Adium1000/Octoglow/.github/frame (1).png

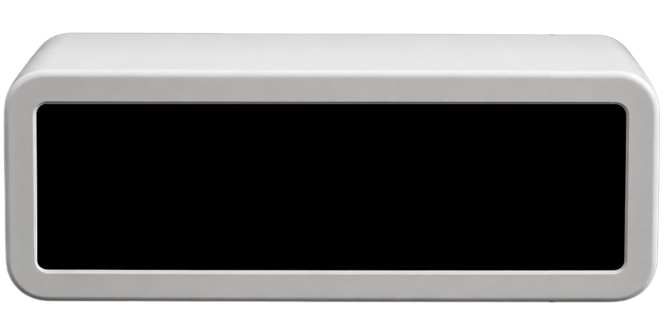
.github/frame (1).png
