Adium1000/Octoglow/.github/frame (2).png

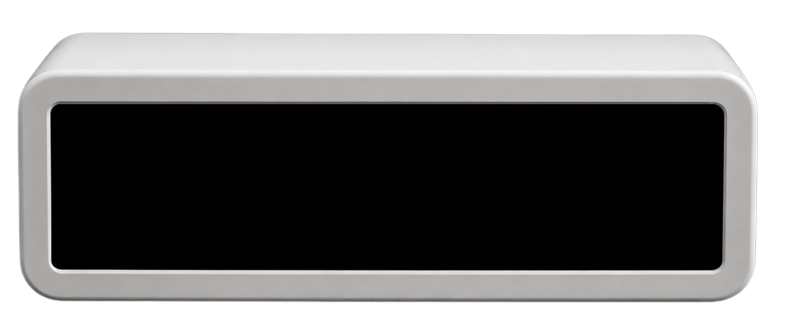
.github/frame (2).png
