Adium1000/Octoglow/.github/frame (3).png

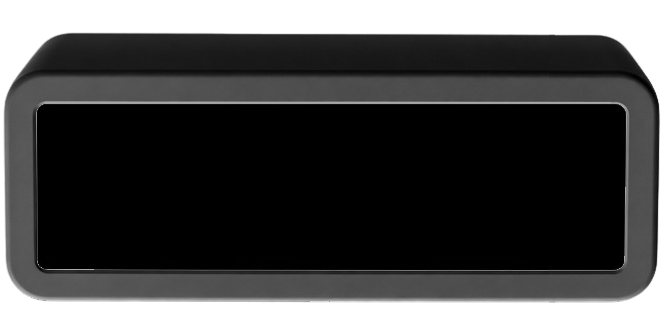
.github/frame (3).png
