Adium1000/Octoglow/Web/ER.png

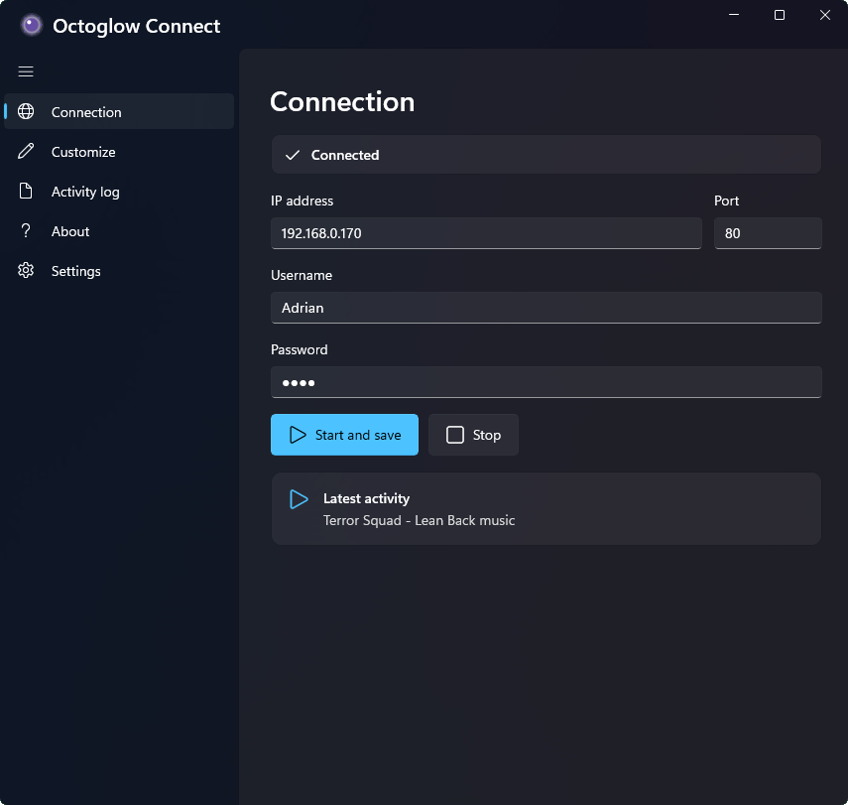
Web/ER.png
