Adium1000/Octoglow/Web/Octoglow_Clock.png

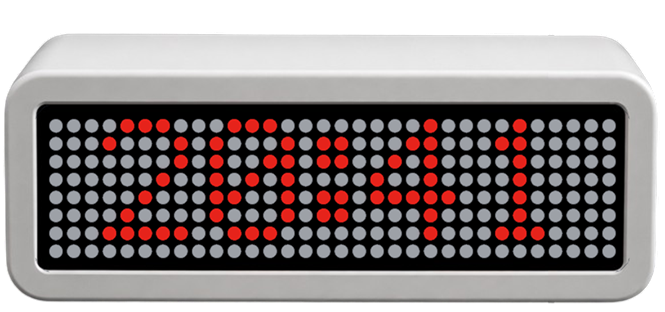
Web/Octoglow_Clock.png
