Adium1000/Octoglow/Firmware/Octoglow/Octoglow.ino

                                                                                
//    ▄▄▄▄                                            ▄▄▄▄                         
//   ██▀▀██               ██                          ▀▀██                         
//  ██    ██   ▄█████▄  ███████    ▄████▄    ▄███▄██    ██       ▄████▄  ██      ██
//  ██    ██  ██▀    ▀    ██      ██▀  ▀██  ██▀  ▀██    ██      ██▀  ▀██ ▀█  ██  █▀
//  ██    ██  ██          ██      ██    ██  ██    ██    ██      ██    ██  ██▄██▄██ 
//   ██▄▄██   ▀██▄▄▄▄█    ██▄▄▄   ▀██▄▄██▀  ▀██▄▄███    ██▄▄▄   ▀██▄▄██▀  ▀██  ██▀ 
//    ▀▀▀▀      ▀▀▀▀▀      ▀▀▀▀     ▀▀▀▀     ▄▀▀▀ ██     ▀▀▀▀     ▀▀▀▀     ▀▀  ▀▀  
//                                          ▀████▀▀                                                                                                          
#include <WiFi.h>
#include <MD_Parola.h>
#include <MD_MAX72xx.h>
#include <SPI.h>
#include <Wire.h>
#include <Adafruit_BMP280.h>
#include <WebServer.h>
#include <Preferences.h>
#include <ArduinoJson.h>
#include <HTTPClient.h>
#include <Update.h>
#include <StreamString.h>
#include <esp_sntp.h>
#include <esp_wifi.h>
#include <esp_sleep.h>
#include "mbedtls/sha256.h"
#include "mbedtls/md.h"

// FIRMWARE VERSION
#define FW_VERSION "0.3"

// FORWARD DECLARATIONS
extern bool provisionMode;
void stopProvisionMode();
bool connectToWiFi(const char* ssid, const char* pass);
void startProvisionMode();
void handleStartAp();
void handleApState();
void handleApSett();
void handleTimeSett();
void handleApPass();
void handleStopAp();
String getApSsid();
String getApPass();
String jsonEscape(const String& in);
void saveSettings();
void applyBrightness();
// AUTH
void handleAuthState();
void handleAuthSetup();
void handleLogin();
void handleLogout();
void handleUpdateAccount();
void handleDashboard();
bool checkAuth();
// SOFTWARE UPDATE (OTA)
void handleSwUpdateUpload();
void handleSwUpdateUploadDone();
void handleBackupRestore();
void handleFactoryReset();
void loadSettings();
void advanceSlot();
void retreatSlot();
int  prevActiveSlot(int from);
void enterSlot(bool playTransition = true);
void drawCircuitTileFrame();
void resumeCircuitTileFromPriority();
void beginC2PCapture();
void finishC2PTransition(uint8_t tileTrans = 0, uint8_t tileSpd = 0);
void beginP2CCapture();
void finishP2CTransition();
void registerTouchTap();
void checkPendingTap();
void executeTouchAction(uint8_t action);
void toggleScreenPower();
bool ipTick();
void startIpShowFromTouch();
void npInit();
void rebuildNowPlayingBuf();
int  nextActiveSlot(int from);
void sortItems();
bool higherPriorityTileActive(uint8_t id);
void rebuildPriorityOrderFromEts2Order();
String priorityOrderToString();
bool npPriorityTick();
void weatherInit();
void weatherFetch();
void weatherDrawAtPos(int pos);
void currencyInit();
void currencyFetch();
void currencyDrawAtPos(int pos);
void drawCanvas();
String canvasBitmapToHex();
bool   canvasBitmapFromHex(const String& hex);
void   ssInit();
void   ssTick();
void   handleScreensaverSett();
String urlEncode(const String& s);

// STOPWATCH
void swInit();
bool swPriorityTick();
void handleSwStart();
void handleSwStop();
void handleSwState();

// TIMER
void timerInit();
bool timerPriorityTick();
void timerCheckExpiry();
void handleTimerSett();
void handleTimerStart();
void handleTimerPause();
void handleTimerState();

// POWER
void handleWifiInfo();
void handlePower();
void noteActivity();
void sleepWake();
void sleepEnter();
bool powerOffNow();

// ALARM
void alarmInit();
bool alarmPriorityTick();
void alarmStopRinging();
void handleAlarmSett();
void handleAlarmStop();
void handleAlarmState();

// DISPLAY
#define CLK_PIN      3
#define DATA_PIN     1
#define CS_PIN       2
#define MAX_DEVICES  4
#define HARDWARE_TYPE MD_MAX72XX::FC16_HW
#define BRIGHTNESS   4

// Brightness / Dim

uint8_t  curBrightness = BRIGHTNESS;
bool     dimAutoOn     = false;
uint8_t  dimFromH = 22, dimFromM = 0;
uint8_t  dimToH   =  7, dimToM   = 0;
uint8_t  dimLevel  = 1;

// BMP280
#define BMP_SDA 5
#define BMP_SCL 4

// TOUCH
#define TOUCH_PIN     6
#define TOUCH_HOLD_MS 2000
#define DOUBLE_TAP_WINDOW_MS 500

// BUZZER
#define BUZZER_PIN 12
// Which volume a sound answers to. NONE is the main volume, heard only in the
// main slider's own preview; the other four can be set apart.
#define BZ_CAT_NONE  0
#define BZ_CAT_NOTIF 1
#define BZ_CAT_AUTO  2
#define BZ_CAT_ALARM 3
#define BZ_CAT_TOUCH 4

// AP CONFIG
#define AP_SSID "Adrian's Octoglow"
#define AP_PASS ""

// TIME

// TIMEZONE TABLE

struct TzEntry { const char* iana; const char* posix; };
static const TzEntry TZ_TABLE[] PROGMEM = {
  {"Africa/Abidjan", "GMT0"},
  {"Africa/Accra", "GMT0"},
  {"Africa/Addis_Ababa", "EAT-3"},
  {"Africa/Algiers", "CET-1"},
  {"Africa/Cairo", "EET-2"},
  {"Africa/Casablanca", "WET0"},
  {"Africa/Johannesburg", "SAST-2"},
  {"Africa/Lagos", "WAT-1"},
  {"Africa/Nairobi", "EAT-3"},
  {"Africa/Tripoli", "EET-2"},
  {"Africa/Tunis", "CET-1"},
  {"America/Anchorage", "AKST9AKDT,M3.2.0,M11.1.0"},
  {"America/Argentina/Buenos_Aires", "ART3"},
  {"America/Bogota", "COT5"},
  {"America/Caracas", "VET4"},
  {"America/Chicago", "CST6CDT,M3.2.0,M11.1.0"},
  {"America/Denver", "MST7MDT,M3.2.0,M11.1.0"},
  {"America/Halifax", "AST4ADT,M3.2.0,M11.1.0"},
  {"America/Lima", "PET5"},
  {"America/Los_Angeles", "PST8PDT,M3.2.0,M11.1.0"},
  {"America/Mexico_City", "CST6CDT,M4.1.0,M10.5.0"},
  {"America/New_York", "EST5EDT,M3.2.0,M11.1.0"},
  {"America/Phoenix", "MST7"},
  {"America/Santiago", "CLT4CLST,M10.2.6/24,M3.2.6/24"},
  {"America/Sao_Paulo", "BRT3BRST,M10.3.0/0,M2.3.0/0"},
  {"America/St_Johns", "NST3:30NDT,M3.2.0,M11.1.0"},
  {"America/Toronto", "EST5EDT,M3.2.0,M11.1.0"},
  {"America/Vancouver", "PST8PDT,M3.2.0,M11.1.0"},
  {"America/Winnipeg", "CST6CDT,M3.2.0,M11.1.0"},
  {"Asia/Almaty", "ALMT-6"},
  {"Asia/Amman", "EET-2EEST,M3.5.4/0,M10.5.5/1"},
  {"Asia/Baghdad", "AST-3"},
  {"Asia/Baku", "AZT-4"},
  {"Asia/Bangkok", "ICT-7"},
  {"Asia/Beirut", "EET-2EEST,M3.5.0/0,M10.5.0/0"},
  {"Asia/Colombo", "IST-5:30"},
  {"Asia/Dhaka", "BST-6"},
  {"Asia/Dubai", "GST-4"},
  {"Asia/Ho_Chi_Minh", "ICT-7"},
  {"Asia/Hong_Kong", "HKT-8"},
  {"Asia/Irkutsk", "IRKT-8"},
  {"Asia/Jakarta", "WIB-7"},
  {"Asia/Jerusalem", "IST-2IDT,M3.4.4/26,M10.5.0"},
  {"Asia/Kabul", "AFT-4:30"},
  {"Asia/Karachi", "PKT-5"},
  {"Asia/Kathmandu", "NPT-5:45"},
  {"Asia/Kolkata", "IST-5:30"},
  {"Asia/Krasnoyarsk", "KRAT-7"},
  {"Asia/Kuala_Lumpur", "MYT-8"},
  {"Asia/Kuwait", "AST-3"},
  {"Asia/Magadan", "MAGT-11"},
  {"Asia/Manila", "PHT-8"},
  {"Asia/Muscat", "GST-4"},
  {"Asia/Nicosia", "EET-2EEST,M3.5.0/3,M10.5.0/4"},
  {"Asia/Novosibirsk", "NOVT-7"},
  {"Asia/Omsk", "OMST-6"},
  {"Asia/Qatar", "AST-3"},
  {"Asia/Riyadh", "AST-3"},
  {"Asia/Seoul", "KST-9"},
  {"Asia/Shanghai", "CST-8"},
  {"Asia/Singapore", "SGT-8"},
  {"Asia/Taipei", "CST-8"},
  {"Asia/Tashkent", "UZT-5"},
  {"Asia/Tbilisi", "GET-4"},
  {"Asia/Tehran", "IRST-3:30IRDT,80/0,264/0"},
  {"Asia/Tokyo", "JST-9"},
  {"Asia/Ulaanbaatar", "ULAT-8"},
  {"Asia/Vladivostok", "VLAT-10"},
  {"Asia/Yakutsk", "YAKT-9"},
  {"Asia/Yekaterinburg", "YEKT-5"},
  {"Asia/Yerevan", "AMT-4"},
  {"Atlantic/Azores", "AZOT1AZOST,M3.5.0/0,M10.5.0/1"},
  {"Atlantic/Cape_Verde", "CVT1"},
  {"Australia/Adelaide", "ACST-9:30ACDT,M10.1.0,M4.1.0/3"},
  {"Australia/Brisbane", "AEST-10"},
  {"Australia/Darwin", "ACST-9:30"},
  {"Australia/Hobart", "AEST-10AEDT,M10.1.0,M4.1.0/3"},
  {"Australia/Melbourne", "AEST-10AEDT,M10.1.0,M4.1.0/3"},
  {"Australia/Perth", "AWST-8"},
  {"Australia/Sydney", "AEST-10AEDT,M10.1.0,M4.1.0/3"},
  {"Europe/Amsterdam", "CET-1CEST,M3.5.0,M10.5.0/3"},
  {"Europe/Athens", "EET-2EEST,M3.5.0/3,M10.5.0/4"},
  {"Europe/Belgrade", "CET-1CEST,M3.5.0,M10.5.0/3"},
  {"Europe/Berlin", "CET-1CEST,M3.5.0,M10.5.0/3"},
  {"Europe/Brussels", "CET-1CEST,M3.5.0,M10.5.0/3"},
  {"Europe/Bucharest", "EET-2EEST,M3.5.0/3,M10.5.0/4"},
  {"Europe/Budapest", "CET-1CEST,M3.5.0,M10.5.0/3"},
  {"Europe/Copenhagen", "CET-1CEST,M3.5.0,M10.5.0/3"},
  {"Europe/Dublin", "GMT0IST,M3.5.0/1,M10.5.0"},
  {"Europe/Helsinki", "EET-2EEST,M3.5.0/3,M10.5.0/4"},
  {"Europe/Istanbul", "TRT-3"},
  {"Europe/Kiev", "EET-2EEST,M3.5.0/3,M10.5.0/4"},
  {"Europe/Kyiv", "EET-2EEST,M3.5.0/3,M10.5.0/4"},
  {"Europe/Lisbon", "WET0WEST,M3.5.0/1,M10.5.0"},
  {"Europe/London", "GMT0BST,M3.5.0/1,M10.5.0"},
  {"Europe/Luxembourg", "CET-1CEST,M3.5.0,M10.5.0/3"},
  {"Europe/Madrid", "CET-1CEST,M3.5.0,M10.5.0/3"},
  {"Europe/Minsk", "FET-3"},
  {"Europe/Moscow", "MSK-3"},
  {"Europe/Oslo", "CET-1CEST,M3.5.0,M10.5.0/3"},
  {"Europe/Paris", "CET-1CEST,M3.5.0,M10.5.0/3"},
  {"Europe/Prague", "CET-1CEST,M3.5.0,M10.5.0/3"},
  {"Europe/Riga", "EET-2EEST,M3.5.0/3,M10.5.0/4"},
  {"Europe/Rome", "CET-1CEST,M3.5.0,M10.5.0/3"},
  {"Europe/Samara", "SAMT-4"},
  {"Europe/Sofia", "EET-2EEST,M3.5.0/3,M10.5.0/4"},
  {"Europe/Stockholm", "CET-1CEST,M3.5.0,M10.5.0/3"},
  {"Europe/Tallinn", "EET-2EEST,M3.5.0/3,M10.5.0/4"},
  {"Europe/Vienna", "CET-1CEST,M3.5.0,M10.5.0/3"},
  {"Europe/Vilnius", "EET-2EEST,M3.5.0/3,M10.5.0/4"},
  {"Europe/Warsaw", "CET-1CEST,M3.5.0,M10.5.0/3"},
  {"Europe/Zurich", "CET-1CEST,M3.5.0,M10.5.0/3"},
  {"Pacific/Auckland", "NZST-12NZDT,M9.5.0,M4.1.0/3"},
  {"Pacific/Fiji", "FJT-12"},
  {"Pacific/Guam", "ChST-10"},
  {"Pacific/Honolulu", "HST10"},
  {"Pacific/Noumea", "NCT-11"},
  {"Pacific/Port_Moresby", "PGT-10"},
  {"UTC", "UTC0"},
  {nullptr, nullptr}
};
static const int TZ_TABLE_SIZE = 119;

const char* ianaToPostfix(const char* iana) {
  for (int i = 0; i < TZ_TABLE_SIZE; i++) {
    if (strcmp(iana, TZ_TABLE[i].iana) == 0)
      return TZ_TABLE[i].posix;
  }
  return nullptr;
}

void applyUtcOffsetFallback(int offset_sec) {
  int absOff = abs(offset_sec);
  int h = absOff / 3600;
  int m = (absOff % 3600) / 60;
  char posix[24];

  if (m == 0) {
    snprintf(posix, sizeof(posix), "UTC%s%d", offset_sec >= 0 ? "-" : "+", h);
  } else {
    snprintf(posix, sizeof(posix), "UTC%s%d:%02d", offset_sec >= 0 ? "-" : "+", h, m);
  }
  setenv("TZ", posix, 1);
  tzset();
  Serial.printf("[TZ] Fallback POSIX: %s\n", posix);
}

void autoDetectTimezone() {
  if (WiFi.status() != WL_CONNECTED) return;
  HTTPClient http;

  http.begin("http://ip-api.com/json/?fields=timezone,offset");
  http.setTimeout(5000);
  int code = http.GET();
  if (code == 200) {
    String body = http.getString();
    StaticJsonDocument<128> doc;
    if (!deserializeJson(doc, body)) {
      const char* iana = doc["timezone"] | "";
      int offset_sec   = doc["offset"]   | 0;
      Serial.printf("[TZ] IP timezone: %s (offset %d)\n", iana, offset_sec);
      const char* posix = ianaToPostfix(iana);
      if (posix) {
        setenv("TZ", posix, 1);
        tzset();
        Serial.printf("[TZ] POSIX: %s\n", posix);
      } else {

        applyUtcOffsetFallback(offset_sec);
      }
    }
  } else {
    Serial.printf("[TZ] ip-api.com eroare %d - ramane TZ anterior\n", code);
  }
  http.end();
}

// NOW PLAYING

#define NOW_PLAYING_TIMEOUT_MS 20000

// CYCLE ITEMS
#define ITEM_HOUR        0
#define ITEM_DATE        1
#define ITEM_TEMP        2
#define ITEM_NOW_PLAYING 3
#define ITEM_WEATHER     4
#define ITEM_MEMENTO     5
#define ITEM_CANVAS      6
#define ITEM_NOTIF       7
#define ITEM_PRESSURE    8
#define ITEM_SCREENSAVER 9
#define ITEM_HOURWEEK    10
#define ITEM_CURRENCY    11
#define ITEM_YOUTUBE     12
#define NUM_ITEMS        12
#define CANVAS_COLS      32

// SCREEN SAVER 
#define SS_ANIM_RANDOM      0
#define SS_ANIM_PONG        1
#define SS_ANIM_FIREWORKS   2
#define SS_ANIM_EQ          3
#define SS_ANIM_COUNT       3

struct CycleItem {
  uint8_t  id;
  bool     enabled;
  uint16_t durationSec;
  uint8_t  order;
};

// GLOBALS
MD_Parola         P  = MD_Parola(HARDWARE_TYPE, DATA_PIN, CLK_PIN, CS_PIN, MAX_DEVICES);
MD_MAX72XX        mx = MD_MAX72XX(HARDWARE_TYPE, DATA_PIN, CLK_PIN, CS_PIN, MAX_DEVICES);
bool gSuppressHwFlash = false;
void screenStreamTick();
static inline void mxCommit() {
  mx.update(gSuppressHwFlash ? MD_MAX72XX::OFF : MD_MAX72XX::ON);
  // The live copy for a subscribed Octoglow Connect; nothing when nobody is.
  screenStreamTick();
}

// The level the panel is running at right now, 0 meaning shut down. /getscreen
// reads it: a panel in shutdown keeps its frame in the buffer but lights none of it.
uint8_t mxPanelLevel = 0;

void applyMaxBrightness(uint8_t uiLevel) {
  mxPanelLevel = uiLevel;
  if (uiLevel == 0) {
    mx.control(MD_MAX72XX::SHUTDOWN, true);
  } else {
    mx.control(MD_MAX72XX::SHUTDOWN, false);
    uint8_t hwIntensity = uiLevel - 1;
    P.setIntensity(hwIntensity);
    mx.control(MD_MAX72XX::INTENSITY, hwIntensity);
  }
}
Adafruit_BMP280   bmp;
WebServer         server(80);
Preferences       prefs;

// AUTH GLOBALS
static char authUser[33]       = "";
static char authPassHash[65]   = "";
static bool authConfigured     = false;

// Cat timp ramane valabil cookie-ul de sesiune (secunde). 30 zile.
#define SESSION_TTL_SECONDS (30UL * 24UL * 3600UL)
// Prag folosit ca sa stim daca ceasul (NTP) e deja sincronizat la bord.
// (orice data reala de dupa 2023 e mai mare decat asta; time(nullptr) inainte
// de sincronizare NTP intoarce valori foarte mici, aproape de epoch 0)
#define TIME_LOOKS_VALID(t) ((t) > 1700000000UL)

static void sha256hex(const char* input, char outHex[65]) {
  uint8_t digest[32];
  mbedtls_sha256_context ctx;
  mbedtls_sha256_init(&ctx);
  mbedtls_sha256_starts(&ctx, 0);
  mbedtls_sha256_update(&ctx, (const unsigned char*)input, strlen(input));
  mbedtls_sha256_finish(&ctx, digest);
  mbedtls_sha256_free(&ctx);
  for (int i = 0; i < 32; i++) sprintf(outHex + i * 2, "%02x", digest[i]);
  outHex[64] = '\0';
}

// HMAC-SHA256(payload) folosind authPassHash-ul curent ca si cheie.
// Nu se stocheaza nimic in plus pe ESP - cheia e deja cea salvata la login.
static void hmacHex(const char* payload, char outHex[65]) {
  uint8_t digest[32];
  const mbedtls_md_info_t* info = mbedtls_md_info_from_type(MBEDTLS_MD_SHA256);
  mbedtls_md_context_t ctx;
  mbedtls_md_init(&ctx);
  mbedtls_md_setup(&ctx, info, 1 /* HMAC */);
  mbedtls_md_hmac_starts(&ctx, (const unsigned char*)authPassHash, strlen(authPassHash));
  mbedtls_md_hmac_update(&ctx, (const unsigned char*)payload, strlen(payload));
  mbedtls_md_hmac_finish(&ctx, digest);
  mbedtls_md_free(&ctx);
  for (int i = 0; i < 32; i++) sprintf(outHex + i * 2, "%02x", digest[i]);
  outHex[64] = '\0';
}

// Comparatie in timp constant, ca sa nu scurgem informatie prin timing.
static bool constTimeEq(const char* a, const char* b) {
  size_t la = strlen(a), lb = strlen(b);
  if (la != lb) return false;
  uint8_t diff = 0;
  for (size_t i = 0; i < la; i++) diff |= (uint8_t)(a[i] ^ b[i]);
  return diff == 0;
}

static void userToHex(const char* user, char* out) {
  size_t n = strlen(user);
  for (size_t i = 0; i < n; i++) sprintf(out + i * 2, "%02x", (uint8_t)user[i]);
  out[n * 2] = '\0';
}

// Construieste un token de sesiune STATELESS: userHex.expiry.hmac
// ESP-ul nu retine nimic despre sesiuni active - orice token se poate
// re-verifica oricand (inclusiv dupa un reboot) doar cu authPassHash-ul
// curent, care e deja incarcat din NVS la boot in loadAuth().
static String makeSessionToken(const char* user) {
  char userHex[70];
  userToHex(user, userHex);
  time_t now = time(nullptr);
  unsigned long expiry = (unsigned long)now + SESSION_TTL_SECONDS;
  char payload[140];
  snprintf(payload, sizeof(payload), "%s.%lu", userHex, expiry);
  char sig[65];
  hmacHex(payload, sig);
  return String(payload) + "." + String(sig);
}

// Verifica un token din cookie fara nicio stare pe ESP.
// Intoarce numele userului daca e valid, altfel sir gol.
static String verifySessionToken(const String& tok) {
  if (!authConfigured || tok.length() == 0) return "";

  int d1 = tok.indexOf('.');
  int d2 = (d1 < 0) ? -1 : tok.indexOf('.', d1 + 1);
  if (d1 < 0 || d2 < 0) return "";

  String userHex   = tok.substring(0, d1);
  String expiryStr = tok.substring(d1 + 1, d2);
  String sig        = tok.substring(d2 + 1);
  if (userHex.length() == 0 || expiryStr.length() == 0 || sig.length() != 64) return "";

  // Fara ceas real (NTP nesincronizat) nu putem verifica expirarea in siguranta.
  time_t now = time(nullptr);
  if (!TIME_LOOKS_VALID(now)) return "";

  unsigned long expiry = strtoul(expiryStr.c_str(), nullptr, 10);
  if ((unsigned long)now > expiry) return "";

  char payload[140];
  snprintf(payload, sizeof(payload), "%s.%s", userHex.c_str(), expiryStr.c_str());
  char expectedSig[65];
  hmacHex(payload, expectedSig);
  if (!constTimeEq(sig.c_str(), expectedSig)) return "";

  // Decodifica userHex -> text si confirma ca e chiar contul configurat acum
  // (daca userul/parola s-au schimbat intre timp, cheia HMAC s-a schimbat si
  // deja am fi picat mai sus la verificarea semnaturii - asta e doar un dublu-check).
  String user;
  for (int i = 0; i + 1 < (int)userHex.length(); i += 2) {
    char byteStr[3] = { userHex[i], userHex[i + 1], 0 };
    user += (char)strtol(byteStr, nullptr, 16);
  }
  if (user != String(authUser)) return "";
  return user;
}

// AP CONFIG 

String getApSsid() {
  prefs.begin("apcfg", true);
  String s = prefs.getString("ssid", "");
  prefs.end();
  if (s.length() == 0) s = AP_SSID;
  return s;
}

String getApPass() {
  prefs.begin("apcfg", true);
  bool hasKey = prefs.isKey("pass");
  String p = hasKey ? prefs.getString("pass", "") : String(AP_PASS);
  prefs.end();
  return p;
}

static void loadAuth() {
  prefs.begin("auth", true);
  String u = prefs.getString("user", "");
  String h = prefs.getString("hash", "");
  prefs.end();
  if (u.length() > 0 && h.length() == 64) {
    strncpy(authUser,     u.c_str(), 32); authUser[32]   = '\0';
    strncpy(authPassHash, h.c_str(), 64); authPassHash[64] = '\0';
    authConfigured = true;
  }
}

static void saveAuth(const char* user, const char* passHash) {
  prefs.begin("auth", false);
  prefs.putString("user", user);
  prefs.putString("hash", passHash);
  prefs.end();
  strncpy(authUser,     user,     32); authUser[32]   = '\0';
  strncpy(authPassHash, passHash, 64); authPassHash[64] = '\0';
  authConfigured = true;
}

static String extractCookieToken() {
  String cookieHdr = server.header("Cookie");
  int idx = cookieHdr.indexOf("sc_tok=");
  if (idx < 0) return "";
  String tok = cookieHdr.substring(idx + 7);
  int end = tok.indexOf(';');
  if (end >= 0) tok = tok.substring(0, end);
  tok.trim();
  return tok;
}

static String getTokenUser() {
  String tok = extractCookieToken();
  if (tok.length() == 0) return "";
  return verifySessionToken(tok);
}

bool checkAuth() {
  if (provisionMode) return true;
  if (getTokenUser().length() == 0) {
    server.send(401, "text/plain", "Neautentificat");
    return false;
  }
  return true;
}

CycleItem items[NUM_ITEMS] = {
  { ITEM_HOUR,        true,  5,  0 },
  { ITEM_DATE,        true,  4,  1 },
  { ITEM_TEMP,        true,  4,  2 },
  { ITEM_NOW_PLAYING, false, 8,  3 },
  { ITEM_WEATHER,     false, 8,  4 },
  { ITEM_MEMENTO,     false, 8,  5 },
  { ITEM_CANVAS,      false, 8,  6 },
  { ITEM_PRESSURE,    false, 8,  7 },
  { ITEM_SCREENSAVER, false, 15,  8 },
  { ITEM_CURRENCY,    false, 8,  9 },
  { ITEM_YOUTUBE,     false, 8, 10 },
  { ITEM_HOURWEEK,    false, 5, 11 },
};

// TILES REMOVED FROM THE MANAGER
//
// One bit per tile: set means the row is not in the Tile Manager, and the tile
// can only come back through the "add" picker. tileHiddenMask is indexed by
// circuit tile id (ITEM_*), prioHiddenMask by PRIORITY_ID_*.
//
// PRIORITY_ID_NOWPLAYING's bit is deliberately never used: Now Playing is one
// tile that lives in either list, so its presence is the ITEM_NOW_PLAYING bit
// in tileHiddenMask no matter which list is showing it, and npIsPriority only
// says which.
uint16_t tileHiddenMask = 0;
uint8_t  prioHiddenMask = 0;

// Whether a circuit tile is in the Tile Manager at all - the same thing as "not
// offered by the add picker". A tile that is not there has nothing to draw on,
// so nothing needs fetching for it.
static inline bool tileInManager(uint8_t id) {
  return !(tileHiddenMask & (1u << id));
}

// A removed tile has no switch left to turn it off with, so removing one has to
// turn it off too. Kept here rather than only in the browser so a restored
// backup, or a client that predates this, cannot leave a tile cycling on the
// panel with no row to stop it from.
static void applyTileHiddenMask() {
  bool anyVisible = false;
  for (int i = 0; i < NUM_ITEMS; i++) {
    if (!(tileHiddenMask & (1u << items[i].id))) { anyVisible = true; break; }
  }
  // Emptying the circuit list entirely would leave the panel with nothing to
  // show and the interface with nothing to put back, so that mask is refused.
  if (!anyVisible) tileHiddenMask = 0;
  for (int i = 0; i < NUM_ITEMS; i++) {
    if (tileHiddenMask & (1u << items[i].id)) items[i].enabled = false;
  }
}

// CANVAS TILE

uint8_t canvasBitmap[CANVAS_COLS] = {0};

uint8_t       currentSlot      = 0;
unsigned long slotStartMs      = 0;

// What the panel is showing at this instant, for the Tile Manager's live
// marker. gLiveTileId is a circuit tile id (ITEM_*) or -1; gLivePrio is the
// wire name of the priority tile that took the frame, or "" when none did.
// Both are set from loop(), where the decision is actually made.
int8_t        gLiveTileId      = -1;
const char*   gLivePrio        = "";
bool          inScrollAnim     = false;
bool          inFadeOut        = false;
bool          inFadeIn         = false;
// Sentinel for "the BMP280 has never given us a usable reading".
#define TEMP_NO_READING (-999)
int           lastTemp         = TEMP_NO_READING;
unsigned long lastTempSampleMs = 0;
#define TEMP_SAMPLE_INTERVAL_MS 5000UL

// Value currently rendered on the temperature tile, so loop() can tell the
// "--" placeholder apart from a real number and swap it out in place.
int           gTempShownValue  = TEMP_NO_READING;

// BMP280 HEALTH
//
// The sensor used to be initialised exactly once in setup() and never checked
// again: if bmp.begin() lost the race at power-up, or the I2C bus later got
// wedged by a slave holding SDA low, every read failed forever and only a
// reboot brought the temperature back. These track the failure state so the
// sensor can be recovered while the clock keeps running.
bool          bmpOk              = false;
uint8_t       bmpFailStreak      = 0;
unsigned long bmpNextRetryMs     = 0;
unsigned long bmpRetryBackoffMs  = 3000UL;
unsigned long lastPressureReadMs = 0;
#define BMP_FAIL_LIMIT       3        // consecutive bad reads before re-init
#define BMP_RETRY_MIN_MS     3000UL
#define BMP_RETRY_MAX_MS     60000UL
#define BMP_READ_INTERVAL_MS 5000UL

unsigned long gLastStaticDrawMs = 0;
bool          gStaticDrawDone   = false;

// HARDWARE MONITOR - main loop instrumentation
//
// The ESP32 exposes no readable CPU-usage counter without enabling the FreeRTOS
// run-time-stats sdkconfig options (off by default in the Arduino core), so no
// usage percentage is reported - inventing one from the loop rate would only
// look precise. What is measured instead is genuinely useful on its own:
// loop() here is a non-blocking state machine, so its iteration rate and, more
// importantly, its worst iteration period tell you directly when something is
// blocking the main loop - which is exactly what makes the web UI sluggish.
unsigned long hwLastLoopUs   = 0;   // timestamp of the previous loop() entry
unsigned long hwLoopCount    = 0;   // iterations in the window being measured
unsigned long hwWindowStart  = 0;
unsigned long hwLoopMaxUs    = 0;   // worst iteration period in the current window
uint32_t      hwLoopsPerSec  = 0;   // last completed window
uint32_t      hwLoopMaxUsLast = 0;

// HTTP TIMING (diagnostic)
//
// server.handleClient() runs the whole request inline, so however long a
// response takes to push is time loop() is not animating the matrix. These
// record the worst offender since boot so it can be read back from /hwstate.
uint32_t      hwHttpMaxUs     = 0;    // longest single handleClient() call
char          hwHttpMaxUri[28] = "";  // which request that was
uint32_t      hwLoopMaxUsEver = 0;    // worst loop iteration since boot
uint32_t      hwPageFull      = 0;    // dashboard sent in full
uint32_t      hwPage304       = 0;    // dashboard answered with a 304
uint32_t      hwPageUs        = 0;    // longest page send
uint32_t      hwStateBuildUs  = 0;    // /state: time spent building + flushing

uint32_t      hwStateUs       = 0;    // longest /state build+send
bool          hwPeaksCleared  = false;

// The configured network name, kept in RAM. /state used to re-open the NVS
// "wifi" namespace on every request just to read this back, which is by far the
// most expensive thing that endpoint did.
String        gWifiSsidCached;

void refreshWifiSsidCache() {
  prefs.begin("wifi", true);
  gWifiSsidCached = prefs.getString("ssid", "");
  prefs.end();
}

// Boot is legitimately busy - WiFi association, NTP, the first weather and
// currency fetches - and those spikes swamped the numbers we actually care
// about. Drop everything recorded in the first 30 seconds, once.
static void hwClearPeaksAfterBoot() {
  if (hwPeaksCleared || millis() < 30000UL) return;
  hwPeaksCleared  = true;
  hwHttpMaxUs     = 0;
  hwLoopMaxUsEver = 0;
  hwPageUs        = 0;
  hwStateUs       = 0;
  hwStateBuildUs  = 0;
  hwHttpMaxUri[0] = '\0';
}

// The peaks above are worst-since-boot, which is the wrong window for chasing
// a stall that happens now and then: one bad moment hours ago hides every later
// one. This lets the interface start a fresh window right before reproducing it.
static void hwResetPeaks() {
  hwHttpMaxUs     = 0;
  hwLoopMaxUsEver = 0;
  hwPageUs        = 0;
  hwStateUs       = 0;
  hwStateBuildUs  = 0;
  hwHttpMaxUri[0] = '\0';
}

// Wraps every handleClient() call in loop() so the cost is attributed.
static void serviceHttp() {
  uint32_t t0 = micros();
  server.handleClient();
  uint32_t dt = micros() - t0;
  if (dt > hwHttpMaxUs) {
    hwHttpMaxUs = dt;
    String u = server.uri();
    // Left empty when there is no URI to name: the interface words that itself,
    // in the language it is showing, where "(fara cerere)" went out as-is.
    strncpy(hwHttpMaxUri, u.c_str(), sizeof(hwHttpMaxUri) - 1);
    hwHttpMaxUri[sizeof(hwHttpMaxUri) - 1] = '\0';
  }
}

// Called at the top of every loop() iteration; a few microseconds of work.
inline void hwMonitorTick() {
  unsigned long nowUs = micros();
  if (hwLastLoopUs) {
    unsigned long dt = nowUs - hwLastLoopUs;
    if (dt > hwLoopMaxUs) hwLoopMaxUs = dt;
    if (dt > hwLoopMaxUsEver) hwLoopMaxUsEver = (uint32_t)dt;
  }
  hwLastLoopUs = nowUs;
  hwLoopCount++;

  unsigned long nowMs = millis();
  if (nowMs - hwWindowStart >= 1000) {
    hwLoopsPerSec   = hwLoopCount;
    hwLoopMaxUsLast = hwLoopMaxUs;
    hwLoopCount   = 0;
    hwLoopMaxUs   = 0;
    hwWindowStart = nowMs;
  }
}



char     nowPlayingBuf[300]    = "";  // "artist - title", and both can be long
char     nowArtist[128]        = "";
char     nowTitle[160]         = "";
unsigned long lastNowPlayingMs = 0;
bool     nowPlayingActive      = false;

uint8_t  npDisplayMode         = 0;

// Adaptive icon: shows a "video" glyph instead of the music note when the
// detected playback source is a video player (set by Octoglow Connect).
bool     npAdaptiveIcon        = true;
bool     npIsVideoSource       = false;

// NOTIFICATIONS 
char     notifBuf[204]         = "";
bool     notifActive           = false;
// When set, this replaces the notification tile's usual glyph for the current
// message only, and is cleared as soon as that message ends.
const uint8_t* notifIconOverride = nullptr;
// True only while the "web interface accessed" alert is the message on screen.
bool     webAccessAlertActive  = false;
bool     hideTileIcons         = false;
bool     notifEnabled          = true;

bool     hideIconDate          = false;
bool     hideIconTemp          = false;
bool     hideIconReminder      = false;
bool     hideIconWeather       = false;
bool     hideIconNotif         = false;
bool     hideIconNowPlaying    = false;
bool     hideIconPressure      = false;
bool     hideIconCurrency      = false;
bool     hideIconYoutube       = false;
bool     hideIconWebAccess     = false;
bool     hideIconIp            = false;

// TILE ICON OVERRIDES (0 = Auto/Default -> tile's own built-in icon)
// Values 1..N select an entry from ICON_CATALOG (see below).
uint8_t  iconSelDate           = 0;
uint8_t  iconSelTemp           = 0;
uint8_t  iconSelReminder       = 0;
uint8_t  iconSelNotif          = 0;
uint8_t  iconSelNpMusic        = 0;
uint8_t  iconSelNpVideo        = 0;
uint8_t  iconSelPressure       = 0;
uint8_t  iconSelCurrency       = 0;
uint8_t  iconSelIp             = 0;
// Weather has several built-in icons (one per condition); each can be
// overridden independently since the tile switches icon automatically.
uint8_t  iconWxSunny           = 0;
uint8_t  iconWxCloud           = 0;
uint8_t  iconWxRain            = 0;
uint8_t  iconWxStorm           = 0;
uint8_t  iconWxSnow            = 0;
uint8_t  iconWxWind            = 0;
uint8_t  iconWxNight           = 0;

uint8_t  scrollType            = 0;

uint8_t  scrollTypeDate         = 0;
uint8_t  scrollTypeTemp         = 0;
uint8_t  scrollTypeReminder     = 0;
uint8_t  scrollTypeWeather      = 0;
uint8_t  scrollTypeNotif        = 0;
uint8_t  scrollTypeNowPlaying   = 0;
uint8_t  scrollTypePressure     = 0;
uint8_t  scrollTypeCurrency     = 0;
uint8_t  scrollTypeYoutube      = 0;
uint8_t  scrollTypeWebAccess    = 0;
uint8_t  scrollTypeStopwatch    = 0;
uint8_t  scrollTypeTimer        = 0;
uint8_t  scrollTypeIp           = 0;

// FONT TYPE (0 = Marymba/default, 1 = Tiko 3x7, 2 = Mako 4x7)
uint8_t  fontType               = 0;

uint8_t  fontTypeDate           = 0;
uint8_t  fontTypeTemp           = 0;
uint8_t  fontTypeReminder       = 0;
uint8_t  fontTypeWeather        = 0;
uint8_t  fontTypeNotif          = 0;
uint8_t  fontTypeNowPlaying     = 0;
uint8_t  fontTypePressure       = 0;
uint8_t  fontTypeCurrency       = 0;
uint8_t  fontTypeYoutube        = 0;
uint8_t  fontTypeWebAccess      = 0;
uint8_t  fontTypeStopwatch      = 0;
uint8_t  fontTypeTimer          = 0;
uint8_t  fontTypeIp             = 0;

// TILE TRANSITION 
uint8_t  tileTransGlobal       = 0;
uint8_t  tileTransHour         = 0;
uint8_t  tileTransDate         = 0;
uint8_t  tileTransTemp         = 0;
uint8_t  tileTransNp           = 0;
uint8_t  tileTransWx           = 0;
uint8_t  tileTransRem          = 0;
uint8_t  tileTransCanvas       = 0;
uint8_t  tileTransPress        = 0;
uint8_t  tileTransSs           = 0;
uint8_t  tileTransCurr         = 0;
uint8_t  tileTransYt           = 0;
uint8_t  tileTransHw           = 0;
uint8_t  tileTransWeb          = 0;
uint8_t  tileTransNotif        = 0;
uint8_t  tileTransEts2         = 0;
uint8_t  tileTransSw           = 0;
uint8_t  tileTransTmr          = 0;
uint8_t  tileTransAlarm        = 0;
uint8_t  tileTransIp           = 0;
uint8_t  tileTransC2P          = 0; // Circuit Tile -> Priority Tile
uint8_t  tileTransP2C          = 0; // Priority Tile -> Circuit Tile

// TILE TRANSITION SPEED
//
// How fast a transition plays, in percent of the pace its effect was drawn
// at: 100 is unchanged, 200 twice as fast, 50 half as fast. Every tileTrans*
// setting above has its own, so whichever setting picked an effect also sets
// its pace; the global slider re-applies one value to all of them. Kept in one
// NVS blob ("trSpeeds") rather than 21 more keys.
#define TRSPD_DEFAULT  100
#define TRSPD_MIN       50
#define TRSPD_MAX      250
#define TRSPD_HOUR      0
#define TRSPD_DATE      1
#define TRSPD_TEMP      2
#define TRSPD_NP        3
#define TRSPD_WX        4
#define TRSPD_REM       5
#define TRSPD_CANVAS    6
#define TRSPD_PRESS     7
#define TRSPD_SS        8
#define TRSPD_CURR      9
#define TRSPD_YT       10
#define TRSPD_HW       11
#define TRSPD_WEB      12
#define TRSPD_NOTIF    13
#define TRSPD_ETS2     14
#define TRSPD_SW       15
#define TRSPD_TMR      16
#define TRSPD_ALARM    17
#define TRSPD_IP       18
#define TRSPD_C2P      19
#define TRSPD_P2C      20
#define TRSPD_COUNT    21

// Suffix of the /state field and the POST argument, "tileTransSpd" + key - the
// same names the effects carry after "tileTrans".
static const char* const TRSPD_KEYS[TRSPD_COUNT] = {
  "Hour", "Date", "Temp", "Np", "Wx", "Rem", "Canvas", "Press", "Ss", "Curr",
  "Yt", "Hw", "Web", "Notif", "Ets2", "Sw", "Tmr", "Alarm", "Ip", "C2P", "P2C"
};

uint8_t  tileTransSpeed        = TRSPD_DEFAULT;  // the global slider
uint8_t  tileTransSpd[TRSPD_COUNT];              // one per setting, filled by loadSettings()

static inline bool scrollIconInBuffer(uint8_t st) { return st == 2 || st == 3; }
static inline bool scrollIsWrap(uint8_t st)       { return st == 1 || st == 3; }

// Key, drawn for the "web interface accessed" alert.
// SCROLL SPEED
//
// Milliseconds between one column step and the next - lower is faster. Every
// tile that can scroll has its own, defaulting to the constant above so nothing
// changes until the user moves a slider.
#define SCROLL_SPEED_DEFAULT 40
#define SCROLL_SPEED_MIN     10
#define SCROLL_SPEED_MAX     120
#define SPD_DATE        0
#define SPD_TEMP        1
#define SPD_REMINDER    2
#define SPD_WEATHER     3
#define SPD_NOTIF       4
#define SPD_NOWPLAYING  5
#define SPD_PRESSURE    6
#define SPD_CURRENCY    7
#define SPD_YOUTUBE     8
#define SPD_WEBACCESS   9
#define SPD_STOPWATCH  10
#define SPD_IP         11
#define SPD_TIMER      12
#define SCROLL_SPEED_COUNT 13

// Suffix used for the NVS key, the /state field and the POST argument, so the
// three stay in step by construction instead of by hand.
static const char* const SPD_KEYS[SCROLL_SPEED_COUNT] = {
  "Date", "Temp", "Reminder", "Weather", "Notif", "NowPlaying", "Pressure",
  "Currency", "Youtube", "WebAccess", "Stopwatch", "Ip", "Timer"
};

uint8_t scrollSpeed = SCROLL_SPEED_DEFAULT;                 // the global slider
uint8_t scrollSpeedTile[SCROLL_SPEED_COUNT] = {
  SCROLL_SPEED_DEFAULT, SCROLL_SPEED_DEFAULT, SCROLL_SPEED_DEFAULT, SCROLL_SPEED_DEFAULT,
  SCROLL_SPEED_DEFAULT, SCROLL_SPEED_DEFAULT, SCROLL_SPEED_DEFAULT, SCROLL_SPEED_DEFAULT,
  SCROLL_SPEED_DEFAULT, SCROLL_SPEED_DEFAULT, SCROLL_SPEED_DEFAULT, SCROLL_SPEED_DEFAULT,
  SCROLL_SPEED_DEFAULT
};

static inline unsigned long spd(uint8_t i) { return (unsigned long)scrollSpeedTile[i]; }

// The alert borrows the notification tile's renderer but has its own look, so
// these pick which set of settings applies to the message currently on screen.
static inline uint8_t notifScrollType() {
  return webAccessAlertActive ? scrollTypeWebAccess : scrollTypeNotif;
}
static inline uint8_t notifFontType() {
  return webAccessAlertActive ? fontTypeWebAccess : fontTypeNotif;
}
static inline bool notifHideIcon() {
  return webAccessAlertActive ? hideIconWebAccess : hideIconNotif;
}
static inline unsigned long notifScrollSpeed() {
  return spd(webAccessAlertActive ? SPD_WEBACCESS : SPD_NOTIF);
}

const uint8_t keyIcon[8] = {
  0b00000000,
  0b01100000,
  0b10010000,
  0b10011111,
  0b10010011,
  0b01100010,
  0b00000000,
  0b00000000
};

const uint8_t notifIcon[8] = {
  0b00000000,
  0b01111110,
  0b11000011,
  0b10100101,
  0b10011001,
  0b10000001,
  0b01111110,
  0b00000000
};

// SHOW IP ADDRESS (Touch Sensor Action)
const uint8_t ipIcon[8] = {
  0b00000001,
  0b00000011,
  0b00001011,
  0b00011011,
  0b01011011,
  0b11011011,
  0b11011011,
  0b00000000
};

// EURO TRUCK SIMULATOR 2

bool     ets2Active            = false;
bool     ets2Enabled           = true;
bool     ets2OrderFirst        = false;

// PRIORITY TILES generic precedence order

#define PRIORITY_ID_NOTIF      0
#define PRIORITY_ID_ETS2       1
#define PRIORITY_ID_NOWPLAYING 2
#define PRIORITY_ID_STOPWATCH  3
#define PRIORITY_ID_TIMER      4
#define PRIORITY_ID_WEB        5
#define PRIORITY_ID_ALARM      6
#define NUM_PRIORITY_IDS       7
// The alarm starts out at the top: it is the one tile that goes off on its own,
// while you are somewhere else, and an alarm ringing behind another tile is an
// alarm you can hear but cannot read. The order stays the user's to change.
uint8_t  priorityOrder[NUM_PRIORITY_IDS] = { PRIORITY_ID_ALARM, PRIORITY_ID_NOTIF, PRIORITY_ID_ETS2, PRIORITY_ID_NOWPLAYING, PRIORITY_ID_STOPWATCH, PRIORITY_ID_TIMER, PRIORITY_ID_WEB };

// ALARM
//
// Three independent alarms. Each has a time, the weekdays it repeats on, a tone
// and a switch. One rings when the clock enters its minute on one of its days,
// and goes on ringing until the touch sensor or the interface stops it.
#define ALARM_COUNT 3

// Days are one bit each, bit 0 = Monday through bit 6 = Sunday. struct tm counts
// from Sunday, so the two are bridged in exactly one place: ALARM_WDAY_BIT.
#define ALARM_WDAY_BIT(tm_wday) ((uint8_t)(1 << (((tm_wday) + 6) % 7)))
#define ALARM_ALL_DAYS 0x7F

// Ringing forever would hold the panel and the buzzer for the rest of the day
// when nobody is there to stop it. After this it gives up on its own; the alarm
// still rings at its next slot.
#define ALARM_MAX_RING_MS 900000UL
// Silence between one pass of the tone and the next.
#define ALARM_TONE_GAP_MS 700UL

struct AlarmCfg {
  uint8_t hour;
  uint8_t minute;
  uint8_t days;
  bool    enabled;
  // Whether this slot holds an alarm at all. Absent is not the same as switched
  // off: an alarm that is off is one you keep and will want again, an absent
  // one is a card that never appears.
  bool    present;
  char    tone[16];
};

AlarmCfg alarms[ALARM_COUNT] = {
  { 7, 30, 0x1F,           false, false, "classic" },
  { 8,  0, 0x60,           false, false, "chimes"  },
  { 9,  0, ALARM_ALL_DAYS, false, false, "morning" },
};

bool          alarmRinging     = false;
int8_t        alarmRingingIdx  = -1;
unsigned long alarmRingStartMs = 0;
bool          alarmWasActive   = false;
unsigned long alarmToneNextMs  = 0;

// One latch per alarm, held for as long as the clock is inside that alarm's
// minute. loop() runs thousands of times a second, so without it an alarm would
// re-fire on every pass; clearing it the moment the minute passes is also what
// lets the same alarm ring again tomorrow, and again next week.
bool          alarmFired[ALARM_COUNT] = { false, false, false };
bool     webAccessEnabled = true;
bool     nowPlayingIsPriority  = false;

bool     npPriorityWasActive   = false;
bool     timerWasActive        = false;

int      ets2Speed             = 0;
unsigned long lastEts2Ms       = 0;
#define ETS2_TIMEOUT_MS 5000

static uint8_t  ets2ColBuf[64];
static int      ets2ColCount  = 0;
static int      ets2LastSpeed = -1;

// STOPWATCH  variables
bool          swRunning       = false;
bool          swWasActive     = false;
unsigned long swStartMs       = 0;
unsigned long swElapsedMs     = 0;

// TIMER variables
char          eventSoundTimer[16] = "calm";

uint32_t      timerDurationSec      = 300;
uint32_t      timerRemainingSnapMs  = 300000UL;
bool          timerRunning          = false;
bool          timerFinished         = false;
bool          timerBlinkOn          = true;
unsigned long timerBlinkLastMs      = 0;
unsigned long timerEndMs            = 0;
uint8_t       timerPreset           = 0;

void timerStart() {
  if (timerRunning || timerFinished) return;
  if (timerRemainingSnapMs == 0) timerRemainingSnapMs = (unsigned long)timerDurationSec * 1000UL;
  timerEndMs  = millis() + timerRemainingSnapMs;
  timerRunning = true;
}

void timerPause() {
  if (!timerRunning) return;
  long rem = (long)(timerEndMs - millis());
  timerRemainingSnapMs = (rem > 0) ? (unsigned long)rem : 0;
  timerRunning = false;
}

void timerDismiss() {
  timerFinished = false;
  timerRemainingSnapMs = (unsigned long)timerDurationSec * 1000UL;
}

uint32_t timerGetRemainingSec() {
  if (timerRunning) {
    long rem = (long)(timerEndMs - millis());
    if (rem < 0) rem = 0;
    return (uint32_t)(rem / 1000);
  }
  return (uint32_t)(timerRemainingSnapMs / 1000);
}

void timerCheckExpiry() {
  if (!timerRunning) return;
  if (timerGetRemainingSec() == 0) {
    timerRunning = false;
    timerRemainingSnapMs = 0;
    timerFinished = true;
    timerBlinkOn = true;
    timerBlinkLastMs = millis();
    nbPlayPreset(eventSoundTimer, BZ_CAT_AUTO);
  }
}

void timerFormatText(char* out, size_t outSize) {
  uint32_t rem = timerGetRemainingSec();
  uint32_t h = rem / 3600, m = (rem % 3600) / 60, s = rem % 60;
  if (h > 0) snprintf(out, outSize, "%02u:%02u:%02u", (unsigned)h, (unsigned)m, (unsigned)s);
  else       snprintf(out, outSize, "%02u:%02u", (unsigned)m, (unsigned)s);
}

unsigned long swGetElapsedMs() {
  return swRunning ? (swElapsedMs + (millis() - swStartMs)) : swElapsedMs;
}

void swFormatFull(char* out, size_t outSize, unsigned long ms) {
  unsigned long h  = ms / 3600000UL;
  unsigned long m  = (ms / 60000UL) % 60UL;
  unsigned long s  = (ms / 1000UL) % 60UL;
  unsigned long cs = (ms / 10UL) % 100UL;
  snprintf(out, outSize, "%02lu:%02lu:%02lu:%02lu", h, m, s, cs);
}

void swFormatAdaptive(char* out, size_t outSize, unsigned long ms) {
  unsigned long h = ms / 3600000UL;
  unsigned long m = (ms / 60000UL) % 60UL;
  unsigned long s = (ms / 1000UL) % 60UL;
  if (h > 0) {
    snprintf(out, outSize, "%02lu:%02lu:%02lu", h, m, s);
  } else {
    snprintf(out, outSize, "%02lu:%02lu", m, s);
  }
}

// WEATHER
char     weatherCity[64]       = "Baia Mare";
char     weatherApiKey[64]     = "";

// OpenWeather keys are 32 hex characters. Rather than pin it to that and break
// the day they change format, this only insists on something a key could be:
// printable ASCII, no spaces, and short enough to store whole. That is already
// enough to reject the bullet characters a masked field used to post back.
static bool wxKeyLooksValid(const String& k) {
  if (k.length() < 8 || k.length() >= sizeof(weatherApiKey)) return false;
  for (unsigned int i = 0; i < k.length(); i++) {
    char c = k[i];
    if (c <= ' ' || c > '~') return false;
  }
  return true;
}
char     weatherLang[8]        = "en";
float    weatherLat            = 47.6575f;
float    weatherLon            = 23.5689f;
char     weatherBuf[128]       = "";
// Which parts of the reading the tile draws. Stored as flags rather than an
// index so the seven combinations need no lookup table, and so the default (all
// three) is the same value the tile behaved as before this existed.
#define WX_SHOW_TEMP 0x01
#define WX_SHOW_HUM  0x02
#define WX_SHOW_DESC 0x04
#define WX_SHOW_ALL  (WX_SHOW_TEMP | WX_SHOW_HUM | WX_SHOW_DESC)
uint8_t  wxPreset              = WX_SHOW_ALL;

float    weatherTempC          = -999;
int      weatherHumidity       = -1;
char     weatherDesc[48]       = "";
unsigned long lastWeatherFetch = 0;
bool     weatherValid          = false;
#define WEATHER_FETCH_INTERVAL_MS  600000UL

const uint8_t sunnyIcon[8] = {
  0b00011000,
  0b01000010,
  0b00011000,
  0b10111101,
  0b10111101,
  0b00011000,
  0b01000010,
  0b00011000
};

const uint8_t cloudIcon[8] = {
  0b00000000,
  0b00111000,
  0b01000110,
  0b10000001,
  0b10000001,
  0b01111110,
  0b00000000,
  0b00000000
};

const uint8_t cloudRainIcon[8] = {
  0b00000000,
  0b00111000,
  0b01000110,
  0b10000001,
  0b10000001,
  0b01111110,
  0b01010100,
  0b00101010
};

const uint8_t cloudLightningIcon[8] = {
  0b00111000,
  0b01000110,
  0b10000001,
  0b10000001,
  0b01111110,
  0b00100100,
  0b01101100,
  0b01001000
};

const uint8_t cloudSnowIcon[8] = {
  0b00111000,
  0b01000110,
  0b10000001,
  0b10010001,
  0b00111000,
  0b01010010,
  0b11100111,
  0b01000010
};

const uint8_t windIcon[8] = {
  0b00001100,
  0b00010010,
  0b00000010,
  0b11111100,
  0b00000000,
  0b11111000,
  0b00000100,
  0b00001000
};

char     weatherCondition[32]  = "";

const uint8_t moonIcon[8] = {
  0b00111100,
  0b01110000,
  0b11100000,
  0b11100000,
  0b11100000,
  0b11100000,
  0b01110000,
  0b00111100
};

// THE CLOCK, READ SAFELY
//
// getLocalTime(info, 0) is not a reliable way to ask what time it is. The core
// writes it as
//
//     uint32_t start = millis();
//     while ((millis() - start) <= ms) { ... return true; }
//     return false;
//
// so with ms == 0 the body runs only if the millisecond counter has not ticked
// between those two millis() calls. That gap is a couple of microseconds out of
// every thousand, which makes roughly one call in several hundred report failure
// on a clock that is perfectly set - and callers that bail on failure then skip
// a draw for no reason at all.
//
// Giving it a non-zero timeout would trade that for a different problem: on a
// clock that has never been set it spends a delay(10) per attempt, and these run
// inside loop(), where the display advances one column per iteration.
//
// This is the same test with neither behaviour: read the clock once, and decide
// from the year whether it has been set.
static bool readLocalTime(struct tm& out) {
  time_t t = time(nullptr);
  localtime_r(&t, &out);
  return out.tm_year > (2016 - 1900);
}

static bool isNight() {
  struct tm ti;
  if (!readLocalTime(ti)) return false;
  int h = ti.tm_hour;
  return (h >= 21 || h < 6);
}

const uint8_t* getWeatherIcon() {
  if (strcasecmp(weatherCondition, "Clear") == 0)
    return isNight() ? resolveTileIcon(iconWxNight, moonIcon) : resolveTileIcon(iconWxSunny, sunnyIcon);
  if (strcasecmp(weatherCondition, "Clouds") == 0)
    return resolveTileIcon(iconWxCloud, cloudIcon);
  if (strcasecmp(weatherCondition, "Rain") == 0 ||
      strcasecmp(weatherCondition, "Drizzle") == 0)
    return resolveTileIcon(iconWxRain, cloudRainIcon);
  if (strcasecmp(weatherCondition, "Thunderstorm") == 0)
    return resolveTileIcon(iconWxStorm, cloudLightningIcon);
  if (strcasecmp(weatherCondition, "Snow") == 0)
    return resolveTileIcon(iconWxSnow, cloudSnowIcon);
  if (strcasecmp(weatherCondition, "Wind") == 0   ||
      strcasecmp(weatherCondition, "Mist") == 0   ||
      strcasecmp(weatherCondition, "Fog") == 0    ||
      strcasecmp(weatherCondition, "Haze") == 0   ||
      strcasecmp(weatherCondition, "Smoke") == 0  ||
      strcasecmp(weatherCondition, "Dust") == 0   ||
      strcasecmp(weatherCondition, "Sand") == 0   ||
      strcasecmp(weatherCondition, "Ash") == 0    ||
      strcasecmp(weatherCondition, "Squall") == 0 ||
      strcasecmp(weatherCondition, "Tornado") == 0)
    return resolveTileIcon(iconWxWind, windIcon);

  return resolveTileIcon(iconWxCloud, cloudIcon);
}

uint8_t  tempUnit              = 0;

uint8_t  hourFormat            = 0;
bool     hourLeadingZero       = false;   // 2:30 -> 02:30

// HOUR AND WEEKDAY TILE
//
// Its own copy of the hour options, so it can run 12h next to a 24h Hour tile,
// plus the one-row bar that goes with the weekday.
#define HW_BAR_STATIC    0   // a fixed underline
#define HW_BAR_SECONDS   1   // fills up across the minute
#define HW_BAR_BELOW     0
#define HW_BAR_ABOVE     1
uint8_t  hwFormat              = 0;       // 0 = 24h, 1 = 12h
bool     hwLeadZero            = false;
uint8_t  hwBarMode             = HW_BAR_SECONDS;
uint8_t  hwBarPos              = HW_BAR_BELOW;
bool     hwSwap                = false;   // day on the left, time on the right

// DEFAULT START MODE
//
// Which radio the clock comes up on after a power cut. Choosing AP also keeps
// the tile loop running there: the access point stops being a repair hatch and
// becomes how the clock normally lives, for anyone with no router to put it on.
// Purely an interface preference: with it off, the web interface leaves out the
// rows it would otherwise show dimmed - a tile that needs the internet while the
// access point is up, an event sound whose tile is switched off, the update
// check in AP mode. Kept on the device so it travels with the user rather than
// with the browser.
bool     showGrayedContent     = true;

// Marks the row the panel is showing right now, in the Tile Manager.
bool     liveTileHighlight     = true;

// Dark mode and the interface language. Neither changes anything the device
// does - they sit next to accentColor purely so the interface looks the same
// from whichever browser the user opens it in. The browser keeps its own
// localStorage copy as well, to paint the right theme before /state arrives.
bool     webUiDark             = true;
char     webUiLang[3]          = "ro";
// Forma ramelor de iconita din interfata: 0 cerc, 1 patrat rotunjit, 2 dala,
// 3 squircle.
uint8_t  webUiShape            = 0;
// Custom interface colours as "bgDark,cardDark,bgLight,cardLight": each slot is
// empty for the theme's own colour, or #rrggbb. Stored as sent - the browser
// works the rest of the surfaces out from them.
char     webUiColors[32]       = "";

#define START_MODE_WIFI 0
#define START_MODE_AP   1
uint8_t  defaultStartMode      = START_MODE_WIFI;

// True while the panel belongs to the AP badge rather than to the tiles. Every
// early return in loop() goes through this, so the one exception - AP picked as
// the start mode - is stated once instead of thirty-four times.
static inline bool tileLoopSuspended() {
  return provisionMode && defaultStartMode != START_MODE_AP;
}

// NETWORK TIME
//
// On by default: NTP keeps the clock right on its own. Switched off, nothing
// writes the RTC but the user - and since there is no battery behind it, the
// time is genuinely lost at every restart and has to be typed in again.
bool     netTimeSync           = true;

// With no valid clock verifySessionToken() refuses to judge a cookie's expiry,
// so every session is rejected and the page that sets the time is the one page
// nobody can reach. Boot manual mode on a plausible date instead of 1970.
#define MANUAL_TIME_FALLBACK 1767225600UL   // 2026-01-01 00:00:00

// SNTP would otherwise walk over a hand-set clock at its next poll.
static void stopNtp() {
  if (esp_sntp_enabled()) esp_sntp_stop();
}

static void seedManualClock() {
  if (TIME_LOOKS_VALID(time(nullptr))) return;
  struct timeval tv;
  tv.tv_sec  = (time_t)MANUAL_TIME_FALLBACK;
  tv.tv_usec = 0;
  settimeofday(&tv, nullptr);
}

// mktime() reads the fields as local time in whatever TZ is active and
// localtime_r() turns them back into the same fields, so what the user types is
// exactly what the tiles show - no offset arithmetic on either side.
static bool applyManualTime(int y, int mo, int d, int h, int mi, int s) {
  if (y < 2024 || y > 2099 || mo < 1 || mo > 12 || d < 1 || d > 31 ||
      h < 0 || h > 23 || mi < 0 || mi > 59 || s < 0 || s > 59) return false;
  struct tm t;
  memset(&t, 0, sizeof(t));
  t.tm_year  = y - 1900;
  t.tm_mon   = mo - 1;
  t.tm_mday  = d;
  t.tm_hour  = h;
  t.tm_min   = mi;
  t.tm_sec   = s;
  t.tm_isdst = -1;
  time_t e = mktime(&t);
  if (e <= 0) return false;
  // mktime normalises out-of-range days (32 Jan becomes 1 Feb); reject that
  // rather than silently storing a date the user did not ask for.
  if (t.tm_mday != d || t.tm_mon != mo - 1) return false;
  struct timeval tv;
  tv.tv_sec  = e;
  tv.tv_usec = 0;
  settimeofday(&tv, nullptr);
  return true;
}

uint8_t  dateFormat            = 2;
uint8_t  dateLang              = 0;  // 0 = English, 1 = Romanian (used only by dateFormat 4 "Mon 11")
char     customDateFmt[24]     = "DD/MM/YYYY";  // used only by dateFormat 5 (custom)

enum NpState {
  NP_SHOW_START,
  NP_PAUSE_BEFORE_RIGHT,
  NP_SCROLL_RIGHT,
  NP_PAUSE_AFTER_RIGHT,
  NP_SCROLL_LEFT,
  NP_PAUSE_BEFORE_NEXT,
  NP_PAUSE_SHORT,
  NP_SCROLL_WRAP
};
NpState       npState         = NP_SHOW_START;
unsigned long npPauseStartMs  = 0;
#define NP_PAUSE_MS 1000

#define SCROLL_WRAP_PASSES 2
static int npWrapPass = 0;

NpState       wxState         = NP_SHOW_START;
unsigned long wxPauseStartMs  = 0;
static int    wxWrapPass      = 0;

NpState       notifState       = NP_SHOW_START;
unsigned long notifPauseMs     = 0;
// Room for the whole text in the widest font (6 columns a letter with the
// gap) plus the icon. At 512 anything past ~85 characters was cut off.
#define NOTIF_COL_MAX 1250
static uint8_t  notifColBuf[NOTIF_COL_MAX];
static int      notifColCount  = 0;
static int      notifScrollPos = 0;
static unsigned long notifLastScrollMs = 0;
static int      notifWrapPass  = 0;
static uint8_t  wxColBuf[512];
static int      wxColCount  = 0;
static int      wxScrollPos = 0;
static unsigned long wxLastScrollMs = 0;

// SHOW IP ADDRESS (Touch Sensor Action)
char          ipBuf[24]          = "";
bool          ipShowActive       = false;
NpState       ipState            = NP_SHOW_START;
unsigned long ipPauseMs          = 0;
static uint8_t  ipColBuf[128];
static int      ipColCount       = 0;
static int      ipScrollPos      = 0;
static unsigned long ipLastScrollMs = 0;
static int      ipWrapPass       = 0;

bool          provisionMode    = false;

// POWER
//
// sleepActive is the panel being dark while everything else carries on: the
// web server answers, Octoglow Connect still gets through, and anything that
// arrives counts as a reason to light back up. Power Off is a different thing
// entirely and does not live in a flag - it is a deep sleep the device only
// comes out of by being held.
bool          sleepActive      = false;
bool          autoSleepOn      = false;
uint32_t      autoSleepSec     = 1800;
unsigned long lastActivityMs   = 0;
// Long enough that a hand passing the pad is not a power button, short enough
// that nobody thinks the clock is broken.
#define POWER_ON_HOLD_MS 1500

bool          buzzerOn         = true;
uint8_t       buzzerVolume     = 80;
// A level per category. The main volume sets all four at once, the way the
// global transition speed sets every tile; they can then be moved apart.
uint8_t       buzzVolNotif     = 80;
uint8_t       buzzVolAuto      = 80;
uint8_t       buzzVolAlarm     = 80;
uint8_t       buzzVolTouch     = 80;
char          buzzerPreset[16] = "calm";
char          eventSoundTile[16]  = "calm";
char          eventSoundWifi[16]  = "urgent";
char          eventSoundNotif[16] = "soft";
char          eventSoundWeb[16]   = "soft";
char          eventSoundEts2[16]  = "urgent";
char          eventSoundTouch[16] = "soft";
char          accentColor[8]      = "#d0bcff";
#define ETS2_SPEED_LIMIT 130
bool          ets2SpeedAlertFired = false;
bool          wifiWasConnected    = true;
bool          touchActive      = false;
unsigned long touchStartMs     = 0;
bool          touchShortFired  = false;
uint8_t       touchTapAction       = 8; // default: Show IP Address
uint8_t       touchDoubleTapAction = 0;
bool          tapPending           = false;
unsigned long lastTapReleaseMs     = 0;
bool          touchScreenOff       = false;

char displayBuf[32];

// BUZZER OUTPUT
//
// The notes are played by the RMT peripheral, from a task of their own.
//
// Timing: a note has to end on time, and the next one start on time, even when
// loop() is busy. A tile transition, a slow request or a WiFi reconnect holds
// loop() for hundreds of milliseconds; a note that only loop() could stop
// droned on through all of it, and a tune that only loop() could advance fell
// apart. buzzTask() walks the queue on its own clock, and each note is a
// counted run of periods that the hardware stops by itself.
//
// Volume: a passive buzzer has no volume line, and narrowing the pulse to make
// it quieter pushes the sound into its upper harmonics, so everything played
// quietly came out at a different pitch. Instead the note keeps its
// half-and-half square shape and its high half is chopped by a 40 kHz carrier.
// The buzzer cannot follow the carrier, only its average, so the level scales
// with the carrier duty and the pitch stays where it was.
//
// Shape: rewriting that duty while a note sounds lets it die away like a
// struck bell or a plucked string instead of stopping dead, which is most of
// the difference between a chime and a beep.
#include "soc/rmt_struct.h"
#include "soc/gpio_struct.h"
#include "soc/gpio_sig_map.h"

#define BUZZ_TICK_HZ       1000000UL  // symbol durations in microseconds
#define BUZZ_CARRIER_HZ    40000UL
#define BUZZ_CARRIER_TICKS 2000       // one carrier period at the 80 MHz RMT group clock
// Never 0 ticks high or low: the register reads 0 as 65536, and the HAL asserts.
#define BUZZ_TICKS_MIN     4
#define BUZZ_TICKS_MAX     1960

// How a note's level moves while it sounds.
#define BZ_ENV_FLAT   0  // on, then off: the original beeps
#define BZ_ENV_PLUCK  1  // struck and quickly gone
#define BZ_ENV_BELL   2  // struck and left to ring
#define BZ_ENV_SWELL  3  // rises, then fades

static portMUX_TYPE nbMux = portMUX_INITIALIZER_UNLOCKED;
static bool    buzzReady        = false;
static int     buzzCarrierTicks = -2;  // -1 carrier off, -2 not known
static int8_t  buzzRmtCh        = -1;  // the RMT channel on the pin, -1 unknown

static uint8_t buzzCatVolume(uint8_t cat) {
  uint8_t v;
  switch (cat) {
    case BZ_CAT_NOTIF: v = buzzVolNotif; break;
    case BZ_CAT_AUTO:  v = buzzVolAuto;  break;
    case BZ_CAT_ALARM: v = buzzVolAlarm; break;
    case BZ_CAT_TOUCH: v = buzzVolTouch; break;
    default:           v = buzzerVolume; break;
  }
  return v > 100 ? 100 : v;
}

static bool buzzBegin() {
  if (buzzReady) return true;
  if (!rmtInit(BUZZER_PIN, RMT_TX_MODE, RMT_MEM_NUM_BLOCKS_1, BUZZ_TICK_HZ)) return false;
  buzzReady        = true;
  buzzCarrierTicks = -2;
  // The Arduino layer does not say which channel it took; the GPIO matrix does.
  uint32_t sel = GPIO.func_out_sel_cfg[BUZZER_PIN].func_sel;
  buzzRmtCh = (sel >= RMT_SIG_OUT0_IDX && sel <= RMT_SIG_OUT3_IDX) ? (int8_t)(sel - RMT_SIG_OUT0_IDX) : -1;
  return true;
}

// Between notes, through the driver. It reaches the pin when the next note starts.
static void buzzCarrierSet(int ticks) {
  if (ticks == buzzCarrierTicks) return;
  bool ok;
  if (ticks < 0) {
    ok = rmtSetCarrier(BUZZER_PIN, false, false, 0, 0.5f);
  } else {
    // The third argument is polarity_active_low: false puts the carrier on the
    // high half of the note. The half tick keeps the driver's truncation from
    // landing one below.
    ok = rmtSetCarrier(BUZZER_PIN, true, false, BUZZ_CARRIER_HZ, (ticks + 0.5f) / BUZZ_CARRIER_TICKS);
  }
  buzzCarrierTicks = ok ? ticks : -2;
}

// While a note sounds. The driver has no call for this, so the duty goes
// straight into the register, followed by the channel's synchronisation bit
// that carries configuration across to the RMT clock domain - the same bit the
// driver sets to start or stop a transmission. The critical section keeps the
// RMT interrupt, which lives on this core, off CONF0 while it is written.
static void buzzCarrierLive(int ticks) {
  if (ticks == buzzCarrierTicks) return;
  if (buzzRmtCh < 0 || buzzCarrierTicks < 0) { buzzCarrierSet(ticks); return; }
  portENTER_CRITICAL(&nbMux);
  RMT.chncarrier_duty[buzzRmtCh].val = ((uint32_t)ticks << 16) | (uint32_t)(BUZZ_CARRIER_TICKS - ticks);
  RMT.chnconf0[buzzRmtCh].conf_update_chn = 1;
  portEXIT_CRITICAL(&nbMux);
  buzzCarrierTicks = ticks;
}

static int buzzTicksFor(float amp) {
  int t = (int)(amp * BUZZ_CARRIER_TICKS + 0.5f);
  if (t < BUZZ_TICKS_MIN) t = BUZZ_TICKS_MIN;
  if (t > BUZZ_TICKS_MAX) t = BUZZ_TICKS_MAX;
  return t;
}

// The level t ms into a note dur ms long, 1 being the note's full volume.
static float buzzEnvelope(uint8_t env, uint32_t t, uint16_t dur) {
  float x = dur ? (float)t / dur : 1.0f;
  if (x > 1.0f) x = 1.0f;
  switch (env) {
    case BZ_ENV_PLUCK: return expf(-3.5f * x);  // ends near 3 %
    case BZ_ENV_BELL:  return expf(-1.8f * x);  // still ringing at 16 %
    case BZ_ENV_SWELL: return x < 0.35f ? 0.4f + 0.6f * x / 0.35f : 1.0f - 0.85f * (x - 0.35f) / 0.65f;
    default:           return 1.0f;
  }
}

// An empty looping write cuts off whatever is sounding; the pin drops to its
// idle level, low.
static void buzzSilence() {
  if (buzzReady) rmtWriteLooping(BUZZER_PIN, NULL, 0);
}

// Starts a note. Returns its full-volume carrier amplitude, or a negative
// number when nothing is sounding: a rest, or a category turned down to 0.
static float buzzStartNote(uint16_t freq, uint16_t durMs, uint8_t env, uint8_t cat) {
  uint8_t vol = buzzCatVolume(cat);
  if (freq == 0 || durMs == 0 || vol == 0) { buzzSilence(); return -1.0f; }
  if (!buzzBegin()) return -1.0f;
  // Loudness falls away far more slowly than the number does, so the setting
  // is squared: 50 drives the buzzer at a quarter, about -12 dB.
  float peak = (vol / 100.0f) * (vol / 100.0f);
  // A flat note at full volume needs no carrier: that is the plain square wave
  // tone() used to play. A shaped note keeps it on so its level can move.
  if (env == BZ_ENV_FLAT && vol >= 100) buzzCarrierSet(-1);
  else                                  buzzCarrierSet(buzzTicksFor(peak * buzzEnvelope(env, 0, durMs)));
  if (freq < 20)    freq = 20;     // half a period has to fit in 15 bits of µs
  if (freq > 20000) freq = 20000;
  uint32_t period = (BUZZ_TICK_HZ + freq / 2) / freq;
  static rmt_data_t sym;
  sym.level0 = 1; sym.duration0 = period / 2;
  sym.level1 = 0; sym.duration1 = period - period / 2;
  uint32_t cycles = ((uint32_t)durMs * 1000UL + period / 2) / period;
  // One cycle would go out as a one-shot write, and the next note could not
  // cut that short. Starting a repeated write cancels the one before it.
  if (cycles < 2) cycles = 2;
  rmtWriteRepeated(BUZZER_PIN, &sym, 1, cycles);
  return peak;
}

// BUZZER QUEUE
//
// loop() and the web handlers queue notes, buzzTask() plays them, and nbMux
// covers everything the two share. Each note carries the category whose volume
// it plays at; nbEnqCat is the one being queued, and only loop() touches it.
#define NB_QUEUE_MAX 64
struct NbNote { uint16_t freq; uint16_t dur; uint8_t env; uint8_t cat; };
static NbNote  nbQueue[NB_QUEUE_MAX];
static uint8_t nbHead     = 0;
static uint8_t nbTail     = 0;
static bool    nbStopReq  = false;
static bool    nbNoteOn   = false;  // a note, or the gap after it, is under way
static bool    nbShutReq  = false;
static volatile bool nbShutDone = false;
static uint8_t nbEnqCat   = BZ_CAT_NONE;
static TaskHandle_t buzzTaskH = NULL;

static void buzzWake() {
  if (buzzTaskH) xTaskNotifyGive(buzzTaskH);
}

static void nbEnqueueEnv(uint16_t freq, uint16_t dur, uint8_t env) {
  portENTER_CRITICAL(&nbMux);
  uint8_t next = (nbTail + 1) % NB_QUEUE_MAX;
  if (next != nbHead) {
    nbQueue[nbTail] = { freq, dur, env, nbEnqCat };
    nbTail = next;
  }
  portEXIT_CRITICAL(&nbMux);
  buzzWake();
}

static void nbEnqueue(uint16_t freq, uint16_t dur) {
  nbEnqueueEnv(freq, dur, BZ_ENV_FLAT);
}

// Empties the queue and cuts off whatever is sounding.
static void nbStop() {
  portENTER_CRITICAL(&nbMux);
  nbHead = nbTail = 0;
  nbStopReq = true;
  portEXIT_CRITICAL(&nbMux);
  buzzWake();
}

// Anything queued, sounding, or about to be cut off.
static bool nbBusy() {
  portENTER_CRITICAL(&nbMux);
  bool busy = nbHead != nbTail || nbNoteOn || nbStopReq;
  portEXIT_CRITICAL(&nbMux);
  return busy;
}

// A note holds the queue for its length plus a 5 ms gap. A shaped note is
// revisited every 3 ms to move its level; otherwise the task sleeps until the
// note is over or something new is queued.
static void buzzTask(void*) {
  unsigned long start = 0;
  uint16_t dur = 0, span = 0;
  uint8_t  env = BZ_ENV_FLAT;
  float    peak = -1.0f;
  for (;;) {
    unsigned long now = millis();
    NbNote n = { 0, 0, 0, 0 };
    bool shut, stop = false, have = false;
    portENTER_CRITICAL(&nbMux);
    shut = nbShutReq;
    if (nbStopReq) { nbStopReq = false; nbNoteOn = false; stop = true; }
    if (nbNoteOn && now - start >= span) nbNoteOn = false;
    if (!shut && !nbNoteOn && nbHead != nbTail) {
      n = nbQueue[nbHead];
      nbHead = (nbHead + 1) % NB_QUEUE_MAX;
      nbNoteOn = have = true;
    }
    bool idle = !nbNoteOn;
    portEXIT_CRITICAL(&nbMux);

    if (shut) {
      buzzSilence();
      if (buzzReady) { rmtDeinit(BUZZER_PIN); buzzReady = false; }
      nbShutDone = true;
      vTaskSuspend(NULL);
    }
    if (have) {
      start = now; dur = n.dur; span = n.dur + 5; env = n.env;
      peak = buzzStartNote(n.freq, n.dur, n.env, n.cat);
    } else if (stop) {
      peak = -1.0f;
      buzzSilence();
    }
    bool shaping = peak >= 0 && env != BZ_ENV_FLAT && now - start < dur;
    if (shaping) buzzCarrierLive(buzzTicksFor(peak * buzzEnvelope(env, now - start, dur)));

    TickType_t wait = portMAX_DELAY;
    if (shaping) {
      wait = pdMS_TO_TICKS(3);
    } else if (!idle) {
      unsigned long el = millis() - start;
      wait = el < span ? pdMS_TO_TICKS(span - el) : 1;
      if (wait == 0) wait = 1;
    }
    ulTaskNotifyTake(pdTRUE, wait);
  }
}

// Silent and released: for boot and for sleep, where the pin must sit low.
static void buzzOff() {
  if (buzzTaskH) {
    portENTER_CRITICAL(&nbMux);
    nbHead = nbTail = 0;
    nbShutReq = true;
    portEXIT_CRITICAL(&nbMux);
    buzzWake();
    for (int i = 0; i < 50 && !nbShutDone; i++) delay(2);
  }
  pinMode(BUZZER_PIN, OUTPUT);
  digitalWrite(BUZZER_PIN, LOW);
}

// Above loop() in priority and on loop()'s core: a busy pass cannot hold a
// note back, and the RMT interrupt the task installs lands on the core that
// buzzCarrierLive() shuts it out of.
static void buzzStartTask() {
  if (buzzTaskH) return;
  xTaskCreatePinnedToCore(buzzTask, "buzzer", 5120, NULL, 2, &buzzTaskH, xPortGetCoreID());
}

// cat is whose volume the preset plays at: BZ_CAT_NOTIF, BZ_CAT_AUTO or
// BZ_CAT_TOUCH.
static void nbPlayPreset(const char* id, uint8_t cat) {
  if (!buzzerOn) return;
  if (strcmp(id, "none") == 0) return;
  nbStop();
  nbEnqCat = cat;
  if (strcmp(id, "calm") == 0) {
    nbEnqueue(1000, 80);
  } else if (strcmp(id, "loud") == 0) {
    nbEnqueue(1500, 130);
  } else if (strcmp(id, "urgent") == 0) {
    for (int i = 0; i < 3; i++) { nbEnqueue(1800, 60); nbEnqueue(0, 15); }
  } else if (strcmp(id, "soft") == 0) {
    nbEnqueue(650, 60);
  } else if (strcmp(id, "double") == 0) {
    nbEnqueue(1200, 70); nbEnqueue(0, 20); nbEnqueue(1200, 70);
  } else if (strcmp(id, "triple") == 0) {
    for (int i = 0; i < 3; i++) { nbEnqueue(1200, 60); nbEnqueue(0, 20); }
  } else if (strcmp(id, "chime") == 0) {
    nbEnqueue(523, 90); nbEnqueue(0, 5); nbEnqueue(659, 90); nbEnqueue(0, 5); nbEnqueue(784, 130);
  } else if (strcmp(id, "bell") == 0) {
    nbEnqueue(1568, 60); nbEnqueue(0, 10); nbEnqueue(1318, 70); nbEnqueue(0, 10); nbEnqueue(1046, 160);
  } else if (strcmp(id, "doorbell") == 0) {
    nbEnqueue(784, 160); nbEnqueue(0, 10); nbEnqueue(659, 220);
  } else if (strcmp(id, "xylophone") == 0) {
    int notes[5] = {659, 784, 880, 988, 1175};
    for (int i = 0; i < 5; i++) { nbEnqueue(notes[i], 55); nbEnqueue(0, 5); }
  } else if (strcmp(id, "harp") == 0) {
    for (int f = 1400; f >= 500; f -= 90) { nbEnqueue(f, 22); nbEnqueue(0, 5); }
  } else if (strcmp(id, "marimba") == 0) {
    nbEnqueue(440, 110); nbEnqueue(0, 5); nbEnqueue(220, 160);
  } else if (strcmp(id, "crystal") == 0) {
    nbEnqueue(1568, 45); nbEnqueue(0, 8); nbEnqueue(1976, 45); nbEnqueue(0, 8); nbEnqueue(2349, 90);
  } else if (strcmp(id, "wave") == 0) {
    for (int f = 400; f <= 1000; f += 60) { nbEnqueue(f, 15); }
    for (int f = 1000; f >= 400; f -= 60) { nbEnqueue(f, 15); }
  } else if (strcmp(id, "lullaby") == 0) {
    int notes[4] = {784, 659, 587, 523};
    for (int i = 0; i < 4; i++) { nbEnqueue(notes[i], 140); nbEnqueue(0, 10); }
  } else if (strcmp(id, "pingpong") == 0) {
    for (int i = 0; i < 4; i++) { nbEnqueue(i % 2 == 0 ? 1200 : 800, 55); nbEnqueue(0, 10); }
  } else if (strcmp(id, "sos") == 0) {
    for (int i = 0; i < 3; i++) { nbEnqueue(1500, 60); nbEnqueue(0, 60); }
    nbEnqueue(0, 80);
    for (int i = 0; i < 3; i++) { nbEnqueue(1500, 180); nbEnqueue(0, 60); }
    nbEnqueue(0, 80);
    for (int i = 0; i < 3; i++) { nbEnqueue(1500, 60); nbEnqueue(0, 60); }
  } else if (strcmp(id, "siren") == 0) {
    for (int f = 400; f <= 1800; f += 70) nbEnqueue(f, 18);
    for (int f = 1800; f >= 400; f -= 70) nbEnqueue(f, 18);
  } else if (strcmp(id, "klaxon") == 0) {
    for (int i = 0; i < 6; i++) { nbEnqueue(i % 2 == 0 ? 1000 : 1400, 45); nbEnqueue(0, 10); }
  } else if (strcmp(id, "laser") == 0) {
    for (int f = 2500; f >= 300; f -= 100) nbEnqueue(f, 10);
  } else if (strcmp(id, "robot") == 0) {
    int notes[5] = {900, 1300, 700, 1600, 1000};
    for (int i = 0; i < 5; i++) { nbEnqueue(notes[i], 40); nbEnqueue(0, 15); }
  } else if (strcmp(id, "fanfare") == 0) {
    nbEnqueue(523, 90);  nbEnqueue(0, 10);
    nbEnqueue(659, 90);  nbEnqueue(0, 10);
    nbEnqueue(784, 90);  nbEnqueue(0, 10);
    nbEnqueue(1046, 220);
  } else if (strcmp(id, "powerdown") == 0) {
    for (int f = 1200; f >= 200; f -= 50) nbEnqueue(f, 14);
  } else if (strcmp(id, "powerup") == 0) {
    for (int f = 200; f <= 1200; f += 50) nbEnqueue(f, 14);
  } else if (strcmp(id, "heartbeat") == 0) {
    nbEnqueue(150, 80); nbEnqueue(0, 40); nbEnqueue(150, 60); nbEnqueue(0, 220);
    nbEnqueue(150, 80); nbEnqueue(0, 40); nbEnqueue(150, 60);
  } else if (strcmp(id, "scifi") == 0) {
    for (int i = 0; i < 2; i++) {
      for (int f = 600; f <= 1600; f += 80) nbEnqueue(f, 12);
      for (int f = 1600; f >= 600; f -= 80) nbEnqueue(f, 12);
    }
  } else if (strcmp(id, "arcade") == 0) {
    int notes[4] = {800, 1000, 1200, 1600};
    for (int i = 0; i < 4; i++) { nbEnqueue(notes[i], 45); nbEnqueue(0, 8); }
  } else if (strcmp(id, "zen") == 0) {
    nbEnqueue(220, 400);
  } else if (strcmp(id, "bubble") == 0) {
    int notes[5] = {600, 900, 1200, 1500, 1800};
    for (int i = 0; i < 5; i++) { nbEnqueue(notes[i], 30); nbEnqueue(0, 10); }
  } else if (strcmp(id, "whistle") == 0) {
    for (int f = 800; f <= 2000; f += 40) nbEnqueue(f, 12);
  // The shaped ones. Each note is struck and left to fade (PLUCK, BELL) or
  // swells and falls away (SWELL), and they keep to the pentatonic and major
  // intervals, in the octave the buzzer sings best in.
  } else if (strcmp(id, "glass") == 0) {
    nbEnqueueEnv(2637, 120, BZ_ENV_BELL); nbEnqueueEnv(1976, 650, BZ_ENV_BELL);
  } else if (strcmp(id, "musicbox") == 0) {
    nbEnqueueEnv(1047, 110, BZ_ENV_PLUCK); nbEnqueueEnv(1319, 110, BZ_ENV_PLUCK);
    nbEnqueueEnv(1568, 110, BZ_ENV_PLUCK); nbEnqueueEnv(2093, 480, BZ_ENV_BELL);
  } else if (strcmp(id, "kalimba") == 0) {
    nbEnqueueEnv(1568, 150, BZ_ENV_PLUCK); nbEnqueueEnv(1319, 150, BZ_ENV_PLUCK);
    nbEnqueueEnv(1047, 380, BZ_ENV_PLUCK);
  } else if (strcmp(id, "dingdong") == 0) {
    nbEnqueueEnv(1319, 420, BZ_ENV_BELL); nbEnqueueEnv(1047, 750, BZ_ENV_BELL);
  } else if (strcmp(id, "droplet") == 0) {
    nbEnqueueEnv(1568, 50, BZ_ENV_PLUCK); nbEnqueueEnv(2349, 300, BZ_ENV_PLUCK);
  } else if (strcmp(id, "success") == 0) {
    nbEnqueueEnv(784, 90, BZ_ENV_PLUCK);   nbEnqueueEnv(1047, 90, BZ_ENV_PLUCK);
    nbEnqueueEnv(1319, 90, BZ_ENV_PLUCK);  nbEnqueueEnv(1568, 450, BZ_ENV_BELL);
  } else if (strcmp(id, "softping") == 0) {
    nbEnqueueEnv(1760, 800, BZ_ENV_BELL);
  } else if (strcmp(id, "aurora") == 0) {
    nbEnqueueEnv(1047, 280, BZ_ENV_SWELL); nbEnqueueEnv(1568, 560, BZ_ENV_BELL);
  } else if (strcmp(id, "harmony") == 0) {
    nbEnqueueEnv(880, 80, BZ_ENV_PLUCK);   nbEnqueueEnv(1109, 80, BZ_ENV_PLUCK);
    nbEnqueueEnv(1319, 80, BZ_ENV_PLUCK);  nbEnqueueEnv(1760, 550, BZ_ENV_BELL);
  } else if (strcmp(id, "twinkle") == 0) {
    nbEnqueueEnv(2637, 70, BZ_ENV_PLUCK);  nbEnqueueEnv(2093, 70, BZ_ENV_PLUCK);
    nbEnqueueEnv(1568, 70, BZ_ENV_PLUCK);  nbEnqueueEnv(2637, 380, BZ_ENV_BELL);
  } else if (strcmp(id, "boldalert") == 0) {
    for (int i = 0; i < 4; i++) { nbEnqueue(300, 70); nbEnqueue(0, 10); nbEnqueue(1200, 70); nbEnqueue(0, 10); }
  } else {
    nbEnqueue(1000, 80);
  }
}

// ALARM TONES
//
// The presets above are single notifications - a note or two and done. An alarm
// has to carry on until somebody stops it, so each tone here is a phrase that
// alarmToneTick() re-queues for as long as the alarm rings. They go through the
// same nbEnqueue()/buzzTask() pair as the presets; only the repeat is new.
// NB_QUEUE_MAX leaves room for 63 entries, rests included, and no phrase below
// goes past 30.
static void alarmEnqueueTone(const char* id) {
  nbEnqCat = BZ_CAT_ALARM;
  if (strcmp(id, "chimes") == 0) {
    // A four-note chime figure, twice over.
    static const uint16_t n[4] = { 659, 784, 587, 392 };
    for (int r = 0; r < 2; r++)
      for (int i = 0; i < 4; i++) { nbEnqueue(n[i], 260); nbEnqueue(0, 40); }
  } else if (strcmp(id, "morning") == 0) {
    static const uint16_t n[6] = { 523, 659, 784, 659, 784, 1046 };
    for (int r = 0; r < 2; r++)
      for (int i = 0; i < 6; i++) { nbEnqueue(n[i], 190); nbEnqueue(0, 30); }
  } else if (strcmp(id, "radar") == 0) {
    for (int r = 0; r < 4; r++) {
      nbEnqueue(880, 90);   nbEnqueue(0, 30);
      nbEnqueue(1046, 90);  nbEnqueue(0, 30);
      nbEnqueue(1318, 150); nbEnqueue(0, 200);
    }
  } else if (strcmp(id, "insistent") == 0) {
    for (int r = 0; r < 6; r++) { nbEnqueue(2000, 90); nbEnqueue(0, 60); nbEnqueue(1600, 90); nbEnqueue(0, 160); }
  } else if (strcmp(id, "siren") == 0) {
    for (int f = 500; f <= 1500; f += 125) nbEnqueue(f, 60);
    for (int f = 1500; f >= 500; f -= 125) nbEnqueue(f, 60);
  } else if (strcmp(id, "melody") == 0) {
    static const uint16_t n[8] = { 523, 587, 659, 523, 523, 587, 659, 523 };
    for (int i = 0; i < 8; i++) { nbEnqueue(n[i], 220); nbEnqueue(0, 30); }
  } else if (strcmp(id, "sunrise") == 0) {
    // A slow climb up the pentatonic scale, every step left to ring.
    static const uint16_t n[6] = { 1047, 1175, 1319, 1568, 1760, 2093 };
    for (int i = 0; i < 6; i++) nbEnqueueEnv(n[i], i == 5 ? 1100 : 420, BZ_ENV_BELL);
  } else if (strcmp(id, "musicbox") == 0) {
    static const uint16_t n[16] = { 1319, 1568, 2093, 1568, 1760, 1568, 1319, 1047,
                                    1175, 1319, 1568, 1319, 1175, 1047, 1175, 1047 };
    for (int i = 0; i < 15; i++) nbEnqueueEnv(n[i], 230, BZ_ENV_PLUCK);
    nbEnqueueEnv(n[15], 800, BZ_ENV_BELL);
  } else if (strcmp(id, "arpeggio") == 0) {
    static const uint16_t n[8] = { 1047, 1319, 1568, 2093, 2637, 2093, 1568, 1319 };
    for (int r = 0; r < 2; r++)
      for (int i = 0; i < 8; i++) nbEnqueueEnv(n[i], 140, BZ_ENV_PLUCK);
    nbEnqueueEnv(1047, 700, BZ_ENV_BELL);
  } else if (strcmp(id, "birds") == 0) {
    // Short plucked chirps with room between them - a trill, a call, a flutter.
    static const uint16_t a[3] = { 2093, 2349, 2637 };
    static const uint16_t b[4] = { 1976, 2349, 2794, 2349 };
    for (int r = 0; r < 2; r++) {
      for (int i = 0; i < 3; i++) nbEnqueueEnv(a[i], 20, BZ_ENV_PLUCK);
      nbEnqueue(0, 140);
      nbEnqueueEnv(2637, 24, BZ_ENV_PLUCK); nbEnqueueEnv(2349, 40, BZ_ENV_PLUCK);
      nbEnqueue(0, 320);
      for (int i = 0; i < 4; i++) nbEnqueueEnv(b[i], 18, BZ_ENV_PLUCK);
      nbEnqueue(0, 480);
    }
  } else if (strcmp(id, "zen") == 0) {
    nbEnqueueEnv(880, 1000, BZ_ENV_SWELL);  nbEnqueue(0, 120);
    nbEnqueueEnv(1319, 1000, BZ_ENV_SWELL); nbEnqueue(0, 120);
    nbEnqueueEnv(1175, 1000, BZ_ENV_SWELL); nbEnqueue(0, 120);
    nbEnqueueEnv(880, 1400, BZ_ENV_SWELL);
  } else if (strcmp(id, "windchime") == 0) {
    nbEnqueueEnv(2637, 420, BZ_ENV_BELL); nbEnqueueEnv(2093, 320, BZ_ENV_BELL); nbEnqueue(0, 120);
    nbEnqueueEnv(2349, 520, BZ_ENV_BELL); nbEnqueueEnv(1760, 360, BZ_ENV_BELL); nbEnqueue(0, 200);
    nbEnqueueEnv(1568, 620, BZ_ENV_BELL); nbEnqueueEnv(2637, 260, BZ_ENV_BELL);
    nbEnqueueEnv(2093, 800, BZ_ENV_BELL);
  } else if (strcmp(id, "gentle") == 0) {
    // Three soft four-note figures, each a step higher, then one bell.
    static const uint16_t n[3][4] = { { 1047, 1319, 1568, 1319 },
                                      { 1175, 1397, 1760, 1397 },
                                      { 1319, 1568, 2093, 1568 } };
    for (int p = 0; p < 3; p++) {
      for (int i = 0; i < 4; i++) nbEnqueueEnv(n[p][i], 260, BZ_ENV_PLUCK);
      nbEnqueue(0, 200);
    }
    nbEnqueueEnv(2093, 900, BZ_ENV_BELL);
  } else {
    // "classic" and anything unrecognised: the two-tone alarm everybody knows.
    for (int r = 0; r < 7; r++) { nbEnqueue(1200, 130); nbEnqueue(0, 60); nbEnqueue(900, 130); nbEnqueue(0, 60); }
  }
}

// Minutes from now until the next alarm that is switched on, or -1 if there is
// none. It walks forward one day at a time instead of reasoning about the
// calendar, so midnight, the end of the week and "already gone for today" are
// all the same case. Eight steps rather than seven: an alarm set for one day a
// week is exactly a week away when today is that day and the time has passed.
static int alarmMinutesUntilNext(int* outIdx) {
  if (outIdx) *outIdx = -1;
  struct tm ti;
  if (!readLocalTime(ti)) return -1;
  int nowMin = ti.tm_hour * 60 + ti.tm_min;
  int best = -1, bestIdx = -1;
  for (int i = 0; i < ALARM_COUNT; i++) {
    if (!alarms[i].present || !alarms[i].enabled || alarms[i].days == 0) continue;
    int at = alarms[i].hour * 60 + alarms[i].minute;
    for (int d = 0; d <= 7; d++) {
      if (!(alarms[i].days & ALARM_WDAY_BIT((ti.tm_wday + d) % 7))) continue;
      int delta = d * 1440 + at - nowMin;
      if (delta < 0) continue;
      // The minute it is ringing in, or has already rung in, is behind us.
      if (delta == 0 && alarmFired[i]) continue;
      if (best < 0 || delta < best) { best = delta; bestIdx = i; }
      break;
    }
  }
  if (outIdx) *outIdx = bestIdx;
  return best;
}

static void alarmStartRinging(int idx) {
  // An alarm nobody can see is half an alarm.
  sleepWake();
  alarmRinging     = true;
  alarmRingingIdx  = (int8_t)idx;
  alarmRingStartMs = millis();
  alarmToneNextMs  = 0;
  if (buzzerOn) {
    nbStop();
    alarmEnqueueTone(alarms[idx].tone);
  }
}

void alarmStopRinging() {
  if (!alarmRinging) return;
  alarmRinging    = false;
  alarmRingingIdx = -1;
  alarmToneNextMs = 0;
  nbStop();
}

// Feeds the buzzer another pass of the tone once the last one has drained. The
// gap is measured from the moment the queue empties, not from when it started,
// so a long tone and a short one both get the same pause between repeats.
static void alarmToneTick() {
  if (!alarmRinging || !buzzerOn) return;
  if (nbBusy()) { alarmToneNextMs = 0; return; }
  unsigned long now = millis();
  if (alarmToneNextMs == 0) { alarmToneNextMs = now + ALARM_TONE_GAP_MS; return; }
  if ((long)(now - alarmToneNextMs) < 0) return;
  alarmToneNextMs = 0;
  if (alarmRingingIdx >= 0) alarmEnqueueTone(alarms[alarmRingingIdx].tone);
}

// Called every pass through loop(). Everything it decides is a function of the
// wall clock, so a reboot changes nothing: the alarms come back from NVS and the
// first tick after the clock is set picks up where it left off.
static void alarmTick() {
  // Taken out of the Tile Manager means switched off, the same as it does for
  // every other priority tile - and a tile that is gone cannot be silenced.
  if (prioHiddenMask & (1u << PRIORITY_ID_ALARM)) {
    if (alarmRinging) alarmStopRinging();
    return;
  }
  if (alarmRinging && (millis() - alarmRingStartMs >= ALARM_MAX_RING_MS)) alarmStopRinging();

  // Four times a second is ample for something that acts on whole minutes, and
  // it keeps even the cheap clock read off the critical path.
  static unsigned long lastCheckMs = 0;
  unsigned long nowMs = millis();
  if (nowMs - lastCheckMs < 250) return;
  lastCheckMs = nowMs;

  struct tm ti;
  if (!readLocalTime(ti)) return;

  uint8_t todayBit = ALARM_WDAY_BIT(ti.tm_wday);
  for (int i = 0; i < ALARM_COUNT; i++) {
    bool match = alarms[i].present &&
                 alarms[i].enabled &&
                 (alarms[i].days & todayBit) &&
                 ti.tm_hour == alarms[i].hour &&
                 ti.tm_min  == alarms[i].minute;
    if (!match)        { alarmFired[i] = false; continue; }
    if (alarmFired[i]) continue;
    // Two alarms set to the same minute both latch here, but only the first in
    // index order starts ringing: the second would otherwise queue up behind it
    // and ask to be stopped a second time for the same minute.
    alarmFired[i] = true;
    if (!alarmRinging) alarmStartRinging(i);
  }
}

// BUZZER BLOCKING (for non-touch events)

void beepSwitch() {
  if (!buzzerOn) return;
  nbPlayPreset(eventSoundTile, BZ_CAT_AUTO);
}

void beepTouch() {
  if (!buzzerOn) return;
  nbPlayPreset(eventSoundTouch, BZ_CAT_TOUCH);
}

// CUSTOM FONT
const uint8_t FONT[][5] = {
  {0x3E, 0x51, 0x49, 0x45, 0x3E},
  {0x00, 0x42, 0x7F, 0x40, 0x00},
  {0x42, 0x61, 0x51, 0x49, 0x46},
  {0x21, 0x41, 0x45, 0x4B, 0x31},
  {0x18, 0x14, 0x12, 0x7F, 0x10},
  {0x27, 0x45, 0x45, 0x45, 0x39},
  {0x3C, 0x4A, 0x49, 0x49, 0x30},
  {0x01, 0x71, 0x09, 0x05, 0x03},
  {0x36, 0x49, 0x49, 0x49, 0x36},
  {0x06, 0x49, 0x49, 0x29, 0x1E},
};
const uint8_t CHAR_C[5]     = {0x3E, 0x41, 0x41, 0x41, 0x22};
const uint8_t CHAR_F[5]     = {0x7F, 0x09, 0x09, 0x01, 0x01};
const uint8_t CHAR_DEG[5]   = {0x06, 0x09, 0x09, 0x06, 0x00};
const uint8_t CHAR_SPACE[5] = {0x00, 0x00, 0x00, 0x00, 0x00};
const uint8_t CHAR_COLON[2] = {0x36, 0x36};
const uint8_t CHAR_DOT[1]   = {0x40};
// Font mode constants (moved up from below so they're visible to appendGlyphAuto)
#define FONT_MODE_DEFAULT 0
#define FONT_MODE_TIKO    1
#define FONT_MODE_MAKO    2
#define FONT_MODE_COUNT   3
#define TIKO_MAX_COLS 5

// Tiko and Mako are both drawn from a glyph table of our own rather than the
// library font, so every place that asked "is it Tiko?" really means "is it
// one of ours?" - and then has to ask the right table.
uint8_t tikoGetChar(char ch, uint8_t size, uint8_t* buf);
uint8_t makoGetChar(char ch, uint8_t size, uint8_t* buf);
static inline bool isPixelFont(uint8_t m) {
  return m == FONT_MODE_TIKO || m == FONT_MODE_MAKO;
}
static inline uint8_t pixGetChar(uint8_t m, char ch, uint8_t size, uint8_t* buf) {
  return (m == FONT_MODE_MAKO) ? makoGetChar(ch, size, buf) : tikoGetChar(ch, size, buf);
}

static void appendGlyphAuto(uint8_t* buf, int& count, int maxCount, char ch, uint8_t fontMode = FONT_MODE_DEFAULT) {
  if (isPixelFont(fontMode)) {
    uint8_t tmp[TIKO_MAX_COLS];
    uint8_t n = pixGetChar(fontMode, ch, sizeof(tmp), tmp);
    if (n == 0) return;
    for (int i = 0; i < n && count < maxCount; i++) buf[count++] = tmp[i];
    if (count < maxCount) buf[count++] = 0x00;
    return;
  }
  if (ch >= '0' && ch <= '9') {
    const uint8_t* g = FONT[ch - '0'];
    for (int i = 0; i < 5 && count < maxCount; i++) buf[count++] = g[i];
    if (count < maxCount) buf[count++] = 0x00;
  } else if (ch == ':') {
    for (int i = 0; i < 2 && count < maxCount; i++) buf[count++] = CHAR_COLON[i];
    if (count < maxCount) buf[count++] = 0x00;
  } else if (ch == '.') {
    if (count < maxCount) buf[count++] = CHAR_DOT[0];
    if (count < maxCount) buf[count++] = 0x00;
  } else {
    uint8_t tmp[8];
    uint8_t n = mx.getChar(ch, sizeof(tmp), tmp);
    if (n == 0) return;
    for (int i = 0; i < n && count < maxCount; i++) buf[count++] = tmp[i];
    if (count < maxCount) buf[count++] = 0x00;
  }
}


// ============================================================
// TIKO FONT (3x7 custom pixel font) — alternative to the
// library-default "Marymba" font used across all tiles.
// Each glyph is stored as N columns (N=3 for almost every
// character, N=5 only for 'W'); each column byte packs 7 rows,
// bit r (r=0..6, r=0 is the TOP row) -> same column-encoding
// convention as the existing digit FONT[][5] table above, so
// it can be dropped in anywhere getChar()-style output is used.
// ============================================================
struct TikoGlyph {
  char    ch;
  uint8_t cols;
  uint8_t data[TIKO_MAX_COLS];
};

const TikoGlyph TIKO_FONT[] = {
  { '1', 3, { 0x42, 0x7F, 0x40 } },
  { '0', 3, { 0x3E, 0x41, 0x3E } },
  { '2', 3, { 0x62, 0x51, 0x4E } },
  { '3', 3, { 0x41, 0x49, 0x3E } },
  { '4', 3, { 0x0F, 0x08, 0x7F } },
  { '5', 3, { 0x4F, 0x49, 0x31 } },
  { '6', 3, { 0x3E, 0x49, 0x30 } },
  { '7', 3, { 0x01, 0x71, 0x0F } },
  { '8', 3, { 0x3E, 0x49, 0x3E } },
  { '9', 3, { 0x06, 0x49, 0x3E } },
  { 'A', 3, { 0x7E, 0x09, 0x7E } },
  { 'B', 3, { 0x7F, 0x49, 0x3E } },
  { 'C', 3, { 0x3E, 0x41, 0x41 } },
  { 'D', 3, { 0x7F, 0x41, 0x3E } },
  { 'E', 3, { 0x7F, 0x49, 0x41 } },
  { 'F', 3, { 0x7F, 0x09, 0x01 } },
  { 'H', 3, { 0x7F, 0x08, 0x7F } },
  { 'I', 3, { 0x00, 0x7F, 0x00 } },
  { 'J', 3, { 0x40, 0x3F, 0x00 } },
  { 'K', 3, { 0x7F, 0x10, 0x6C } },
  { 'L', 3, { 0x3F, 0x40, 0x40 } },
  { 'G', 3, { 0x3E, 0x41, 0x70 } },
  { 'M', 3, { 0x7F, 0x02, 0x7F } },
  { 'N', 3, { 0x7F, 0x01, 0x7E } },
  { 'O', 3, { 0x3E, 0x41, 0x3E } },
  { 'P', 3, { 0x7F, 0x09, 0x06 } },
  { 'Q', 3, { 0x1E, 0x21, 0x5E } },
  { 'R', 3, { 0x7F, 0x09, 0x76 } },
  { 'S', 3, { 0x4E, 0x49, 0x31 } },
  { 'T', 3, { 0x01, 0x7F, 0x01 } },
  { 'U', 3, { 0x3F, 0x40, 0x3F } },
  { 'V', 3, { 0x3F, 0x60, 0x3F } },
  { 'W', 5, { 0x3F, 0x40, 0x38, 0x40, 0x3F } },
  { 'X', 3, { 0x67, 0x18, 0x67 } },
  { 'Y', 3, { 0x07, 0x78, 0x07 } },
  { ':', 3, { 0x00, 0x36, 0x00 } },
  { ',', 3, { 0x00, 0x60, 0x00 } },
  { '.', 3, { 0x00, 0x20, 0x00 } },
  { '?', 3, { 0x02, 0x51, 0x0E } },
  { '!', 3, { 0x00, 0x5F, 0x00 } },
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
};
const uint8_t TIKO_FONT_COUNT = sizeof(TIKO_FONT) / sizeof(TIKO_FONT[0]);

// Characters that exist in the pixel-art source but are not part
// of the printable glyph table above (used by the temp/pressure
// builders instead of going through tikoGetChar):
const uint8_t TIKO_DEG[3]   = { 0x02, 0x05, 0x02 };  // °
const uint8_t TIKO_MINUS[3] = { 0x08, 0x08, 0x08 };  // -
const uint8_t TIKO_SPACE[2] = { 0x00, 0x00 };        // ' ' (no glyph in source font)

// Drop-in replacement for mx.getChar(ch, size, buf): looks the
// character up in TIKO_FONT (case-insensitive — the source font
// only defines uppercase letters), falls back to a blank space
// glyph for anything unmapped (accented letters, '@', '-', '+',
// '=', '&', '*', '#', '_', '$', etc. are not present in the
// supplied pixel art and are not guessed at here).
uint8_t tikoGetChar(char ch, uint8_t size, uint8_t* buf) {
  if (ch == ' ') {
    uint8_t n = (2 <= size) ? 2 : size;
    for (uint8_t i = 0; i < n; i++) buf[i] = TIKO_SPACE[i];
    return n;
  }
  if (ch == '-') {
    uint8_t n = (3 <= size) ? 3 : size;
    for (uint8_t i = 0; i < n; i++) buf[i] = TIKO_MINUS[i];
    return n;
  }
  char up = (ch >= 'a' && ch <= 'z') ? (ch - 32) : ch;
  for (uint8_t gi = 0; gi < TIKO_FONT_COUNT; gi++) {
    if (TIKO_FONT[gi].ch == up) {
      uint8_t n = (TIKO_FONT[gi].cols <= size) ? TIKO_FONT[gi].cols : size;
      for (uint8_t i = 0; i < n; i++) buf[i] = TIKO_FONT[gi].data[i];
      return n;
    }
  }
  // Unmapped character: fall back to a blank 3-col space so text
  // keeps flowing instead of stalling the buffer.
  uint8_t n = (3 <= size) ? 3 : size;
  for (uint8_t i = 0; i < n; i++) buf[i] = 0x00;
  return n;
}

// ============================================================
// MICRO FONT (3x5) - only for the Hour and Weekday tile, where the
// weekday has to sit next to a full Tiko time. Same column layout
// as TIKO_FONT (bit 0 = top row); W is the only 5-column letter.
// Holds just the capitals the RO/EN weekday names use.
// ============================================================
const TikoGlyph MICRO_FONT[] = {
  { 'A', 3, { 0x1E, 0x05, 0x1E } },
  { 'D', 3, { 0x1F, 0x11, 0x0E } },
  { 'E', 3, { 0x1F, 0x15, 0x11 } },
  { 'F', 3, { 0x1F, 0x05, 0x01 } },
  { 'H', 3, { 0x1F, 0x04, 0x1F } },
  { 'I', 3, { 0x11, 0x1F, 0x11 } },
  { 'J', 3, { 0x08, 0x10, 0x0F } },
  { 'L', 3, { 0x1F, 0x10, 0x10 } },
  { 'M', 3, { 0x1F, 0x02, 0x1F } },
  { 'N', 3, { 0x1F, 0x01, 0x1E } },
  { 'O', 3, { 0x0E, 0x11, 0x0E } },
  { 'R', 3, { 0x1F, 0x05, 0x1A } },
  { 'S', 3, { 0x12, 0x15, 0x09 } },
  { 'T', 3, { 0x01, 0x1F, 0x01 } },
  { 'U', 3, { 0x1F, 0x10, 0x1F } },
  { 'V', 3, { 0x0F, 0x10, 0x0F } },
  { 'W', 5, { 0x1F, 0x08, 0x04, 0x08, 0x1F } },
};
const uint8_t MICRO_FONT_COUNT = sizeof(MICRO_FONT) / sizeof(MICRO_FONT[0]);

// Case-insensitive like tikoGetChar(); returns 0 for a letter it lacks.
// buf must hold TIKO_MAX_COLS bytes.
static uint8_t microGetChar(char ch, uint8_t* buf) {
  char up = (ch >= 'a' && ch <= 'z') ? (ch - 32) : ch;
  for (uint8_t gi = 0; gi < MICRO_FONT_COUNT; gi++) {
    if (MICRO_FONT[gi].ch == up) {
      memcpy(buf, MICRO_FONT[gi].data, MICRO_FONT[gi].cols);
      return MICRO_FONT[gi].cols;
    }
  }
  return 0;
}
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
void loop() {
  hwMonitorTick();
  hwClearPeaksAfterBoot();
  screenStreamTick();
  handleTouch();

  if (pendingModeSwitch) {
    doPendingModeSwitch();
    return;
  }

  // Changing Default Start Mode while the access point is already up flips this
  // without going through startProvisionMode(), so the badge has to be put back
  // by hand - otherwise the panel keeps whatever tile frame was drawn last.
  static bool tileLoopWasSuspended = false;
  bool tileLoopNowSuspended = tileLoopSuspended();
  if (tileLoopNowSuspended && !tileLoopWasSuspended) drawApScreen();
  tileLoopWasSuspended = tileLoopNowSuspended;

  // Ahead of the early return below: an alarm goes off at its time whether or
  // not the access point happens to be up. The panel belongs to the AP badge
  // while that is showing, so in AP mode the alarm is heard rather than seen -
  // and the touch sensor still stops it.
  alarmTick();
  alarmToneTick();
  autoSleepTick();

  if (tileLoopNowSuspended) {
    // The access point badge is not a tile, so nothing in the manager is live.
    gLiveTileId = -1;
    gLivePrio   = "";
    serviceHttp();
    // settingsFlushTick() sits near the bottom of loop(), behind this return -
    // so for as long as this branch was taken, nothing changed in AP mode ever
    // reached NVS. Deferred writes have to be flushed here too.
    settingsFlushTick();
    return;
  }

  // WiFi Connection Lost detects the connected > disconnected transition.
  // There is no station connection to lose while the access point is up, and
  // wifiWasConnected starts out true - so without this the first iteration
  // after booting into AP announced a drop that never happened. Holding it
  // false also means reconnecting later reads as a clean false -> true, with no
  // spurious alert on the way back.
  if (provisionMode) {
    wifiWasConnected = false;
  } else {
    bool wifiNowConnected = (WiFi.status() == WL_CONNECTED);
    if (wifiWasConnected && !wifiNowConnected) {
      nbPlayPreset(eventSoundWifi, BZ_CAT_AUTO);
      // Something the owner would want to see, so it counts as activity.
      noteActivity();
    }
    wifiWasConnected = wifiNowConnected;
  }

  if (nowPlayingActive && (millis() - lastNowPlayingMs > NOW_PLAYING_TIMEOUT_MS)) {
    nowPlayingActive = false;
    nowPlayingBuf[0] = '\0';
    npPriorityWasActive = false;

    if (!nowPlayingIsPriority && items[currentSlot].id == ITEM_NOW_PLAYING) {
      advanceSlot();
      serviceHttp();
      if (tileLoopSuspended()) return;
      return;
    }
  }

  // Show IP Address (touch action) takes precedence over everything else; it is a
  // short, user-triggered, one-shot display and is not part of the reorderable
  // Priority Tiles order.
  if (ipTick()) {
    // Show IP Address is a touch action, not a row in the manager.
    gLiveTileId = -1;
    gLivePrio   = "";
    serviceHttp();
    if (tileLoopSuspended()) return;
    return;
  }

  // Priority Tiles: the first active tile in the configured order interrupts the normal loop
  for (int pi = 0; pi < NUM_PRIORITY_IDS; pi++) {
    bool handled = false;
    switch (priorityOrder[pi]) {
      // Both slots run the same renderer; webAccessAlertActive decides which
      // one the message on screen belongs to, so each gets its own rank.
      case PRIORITY_ID_NOTIF:      handled = !webAccessAlertActive && notifTick(); break;
      case PRIORITY_ID_WEB:        handled =  webAccessAlertActive && notifTick(); break;
      case PRIORITY_ID_ETS2:       handled = ets2Tick();       break;
      case PRIORITY_ID_NOWPLAYING: handled = npPriorityTick(); break;
      case PRIORITY_ID_STOPWATCH:  handled = swPriorityTick(); break;
      case PRIORITY_ID_TIMER:      handled = timerPriorityTick(); break;
      case PRIORITY_ID_ALARM:      handled = alarmPriorityTick(); break;
    }
    if (handled) {
      gLiveTileId = -1;
      gLivePrio   = priorityIdName(priorityOrder[pi]);
      serviceHttp();
      if (tileLoopSuspended()) return;
      return;
    }
  }

  CycleItem& cur = items[currentSlot];
  gLiveTileId = (int8_t)cur.id;
  gLivePrio   = "";

  if (cur.id == ITEM_NOW_PLAYING) {

    if (notifActive) {
      serviceHttp();
      if (tileLoopSuspended()) return;
      return;
    }
    unsigned long now = millis();
    switch (npState) {

      case NP_SHOW_START:
        break;

      case NP_PAUSE_BEFORE_RIGHT:
        if (now - npPauseStartMs >= NP_PAUSE_MS) {
          if (scrollIsWrap(scrollTypeNowPlaying)) {
            npWrapPass = 0;
            npScrollPos = 0;
            npState = NP_SCROLL_WRAP;
          } else {
            npState = NP_SCROLL_RIGHT;
          }
          npLastScrollMs = now;
        }
        break;

      case NP_SCROLL_WRAP: {
        if (now - npLastScrollMs >= spd(SPD_NOWPLAYING)) {
          npLastScrollMs = now;
          npScrollPos++;
          if (npScrollPos >= npColCount) {
            npWrapPass++;
            if (npWrapPass >= SCROLL_WRAP_PASSES) {
              advanceSlot();
              serviceHttp();
              if (tileLoopSuspended()) return;
              return;
            }
            npScrollPos = -((hideIconNowPlaying || scrollIconInBuffer(scrollTypeNowPlaying)) ? 32 : NP_TEXT_COLS);
          }
          npDrawAtPos(npScrollPos);
        }
        break;
      }

      case NP_SCROLL_RIGHT: {
        int maxPos = npColCount - ((hideIconNowPlaying || scrollIconInBuffer(scrollTypeNowPlaying)) ? 32 : NP_TEXT_COLS);
        if (maxPos <= 0) {
          npState = NP_PAUSE_SHORT;
          npPauseStartMs = now;
          break;
        }
        if (now - npLastScrollMs >= spd(SPD_NOWPLAYING)) {
          npLastScrollMs = now;
          npScrollPos++;
          npDrawAtPos(npScrollPos);
          if (npScrollPos >= maxPos) {
            npScrollPos = maxPos;
            npState = NP_PAUSE_AFTER_RIGHT;
            npPauseStartMs = now;
          }
        }
        break;
      }

      case NP_PAUSE_AFTER_RIGHT:
        if (now - npPauseStartMs >= NP_PAUSE_MS) {
          npState = NP_SCROLL_LEFT;
          npLastScrollMs = now;
        }
        break;

      case NP_SCROLL_LEFT:
        if (now - npLastScrollMs >= spd(SPD_NOWPLAYING)) {
          npLastScrollMs = now;
          npScrollPos--;
          if (npScrollPos <= 0) {
            npScrollPos = 0;
            npDrawAtPos(0);
            npState = NP_PAUSE_BEFORE_NEXT;
            npPauseStartMs = now;
          } else {
            npDrawAtPos(npScrollPos);
          }
        }
        break;

      case NP_PAUSE_BEFORE_NEXT:
        if (now - npPauseStartMs >= NP_PAUSE_MS) {
          advanceSlot();
          serviceHttp();
          if (tileLoopSuspended()) return;
          return;
        }
        break;

      case NP_PAUSE_SHORT:
        if (now - npPauseStartMs >= 4000UL) {
          advanceSlot();
          serviceHttp();
          if (tileLoopSuspended()) return;
          return;
        }
        break;
    }

    serviceHttp();
    if (tileLoopSuspended()) return;
    return;
  }

  // WEATHER SCROLL (identical to NP)
  if (cur.id == ITEM_WEATHER) {
    unsigned long now = millis();
    switch (wxState) {
      case NP_SHOW_START:
        break;
      case NP_PAUSE_BEFORE_RIGHT:
        if (now - wxPauseStartMs >= NP_PAUSE_MS) {
          if (scrollIsWrap(scrollTypeWeather)) {
            wxWrapPass = 0;
            wxScrollPos = 0;
            wxState = NP_SCROLL_WRAP;
          } else {
            wxState = NP_SCROLL_RIGHT;
          }
          wxLastScrollMs = now;
        }
        break;
      case NP_SCROLL_WRAP: {
        if (now - wxLastScrollMs >= spd(SPD_WEATHER)) {
          wxLastScrollMs = now;
          wxScrollPos++;
          if (wxScrollPos >= wxColCount) {
            wxWrapPass++;
            if (wxWrapPass >= SCROLL_WRAP_PASSES) {
              advanceSlot();
              serviceHttp();
              if (tileLoopSuspended()) return;
              return;
            }
            wxScrollPos = -((hideIconWeather || scrollIconInBuffer(scrollTypeWeather)) ? 32 : NP_TEXT_COLS);
          }
          weatherDrawAtPos(wxScrollPos);
        }
        break;
      }
      case NP_SCROLL_RIGHT: {
        int maxPos = wxColCount - ((hideIconWeather || scrollIconInBuffer(scrollTypeWeather)) ? 32 : NP_TEXT_COLS);
        if (maxPos <= 0) {
          wxState = NP_PAUSE_SHORT;
          wxPauseStartMs = now;
          break;
        }
        if (now - wxLastScrollMs >= spd(SPD_WEATHER)) {
          wxLastScrollMs = now;
          wxScrollPos++;
          weatherDrawAtPos(wxScrollPos);
          if (wxScrollPos >= maxPos) {
            wxScrollPos = maxPos;
            wxState = NP_PAUSE_AFTER_RIGHT;
            wxPauseStartMs = now;
          }
        }
        break;
      }
      case NP_PAUSE_AFTER_RIGHT:
        if (now - wxPauseStartMs >= NP_PAUSE_MS) {
          wxState = NP_SCROLL_LEFT;
          wxLastScrollMs = now;
        }
        break;
      case NP_SCROLL_LEFT:
        if (now - wxLastScrollMs >= spd(SPD_WEATHER)) {
          wxLastScrollMs = now;
          wxScrollPos--;
          if (wxScrollPos <= 0) {
            wxScrollPos = 0;
            weatherDrawAtPos(0);
            wxState = NP_PAUSE_BEFORE_NEXT;
            wxPauseStartMs = now;
          } else {
            weatherDrawAtPos(wxScrollPos);
          }
        }
        break;
      case NP_PAUSE_BEFORE_NEXT:
        if (now - wxPauseStartMs >= NP_PAUSE_MS) {
          advanceSlot();
          serviceHttp();
          if (tileLoopSuspended()) return;
          return;
        }
        break;
      case NP_PAUSE_SHORT:
        if (now - wxPauseStartMs >= 4000UL) {
          advanceSlot();
          serviceHttp();
          if (tileLoopSuspended()) return;
          return;
        }
        break;
    }
    serviceHttp();
    if (tileLoopSuspended()) return;
    return;
  }

  // CURRENCY STANDARDS 
  if (cur.id == ITEM_CURRENCY) {
    unsigned long now = millis();
    switch (currState) {
      case NP_SHOW_START:
        break;
      case NP_PAUSE_BEFORE_RIGHT:
        if (now - currPauseMs >= NP_PAUSE_MS) {
          if (scrollIsWrap(scrollTypeCurrency)) {
            currWrapPass = 0;
            currScrollPos = 0;
            currState = NP_SCROLL_WRAP;
          } else {
            currState = NP_SCROLL_RIGHT;
          }
          currLastScrollMs = now;
        }
        break;
      case NP_SCROLL_WRAP: {
        if (now - currLastScrollMs >= spd(SPD_CURRENCY)) {
          currLastScrollMs = now;
          currScrollPos++;
          if (currScrollPos >= currColCount) {
            currWrapPass++;
            if (currWrapPass >= SCROLL_WRAP_PASSES) {
              advanceSlot();
              serviceHttp();
              if (tileLoopSuspended()) return;
              return;
            }
            currScrollPos = -((hideIconCurrency || scrollIconInBuffer(scrollTypeCurrency)) ? 32 : PRESSURE_TEXT_COLS);
          }
          currencyDrawAtPos(currScrollPos);
        }
        break;
      }
      case NP_SCROLL_RIGHT: {
        int maxPos = currColCount - ((hideIconCurrency || scrollIconInBuffer(scrollTypeCurrency)) ? 32 : PRESSURE_TEXT_COLS);
        if (maxPos <= 0) {
          currState = NP_PAUSE_SHORT;
          currPauseMs = now;
          break;
        }
        if (now - currLastScrollMs >= spd(SPD_CURRENCY)) {
          currLastScrollMs = now;
          currScrollPos++;
          currencyDrawAtPos(currScrollPos);
          if (currScrollPos >= maxPos) {
            currScrollPos = maxPos;
            currState = NP_PAUSE_AFTER_RIGHT;
            currPauseMs = now;
          }
        }
        break;
      }
      case NP_PAUSE_AFTER_RIGHT:
        if (now - currPauseMs >= NP_PAUSE_MS) {
          currState = NP_SCROLL_LEFT;
          currLastScrollMs = now;
        }
        break;
      case NP_SCROLL_LEFT:
        if (now - currLastScrollMs >= spd(SPD_CURRENCY)) {
          currLastScrollMs = now;
          currScrollPos--;
          if (currScrollPos <= 0) {
            currScrollPos = 0;
            currencyDrawAtPos(0);
            currState = NP_PAUSE_BEFORE_NEXT;
            currPauseMs = now;
          } else {
            currencyDrawAtPos(currScrollPos);
          }
        }
        break;
      case NP_PAUSE_BEFORE_NEXT:
        if (now - currPauseMs >= NP_PAUSE_MS) {
          advanceSlot();
          serviceHttp();
          if (tileLoopSuspended()) return;
          return;
        }
        break;
      case NP_PAUSE_SHORT:
        if (now - currPauseMs >= 4000UL) {
          advanceSlot();
          serviceHttp();
          if (tileLoopSuspended()) return;
          return;
        }
        break;
    }
    serviceHttp();
    if (tileLoopSuspended()) return;
    return;
  }
  // SOCIAL COUNTER TILES - same scroll behaviour as the currency tile
  // When the text already fits, nothing below runs: the tile falls through to
  // the generic slot timer at the end of loop(), so it honours its configured
  // display time instead of the scroll machine's own pauses.
  if (socialIndexForItem(cur.id) >= 0 && socNeedsScroll) {
    unsigned long now = millis();
    switch (socState) {
      case NP_SHOW_START:
        break;
      case NP_PAUSE_BEFORE_RIGHT:
        if (now - socPauseMs >= NP_PAUSE_MS) {
          if (scrollIsWrap(scrollTypeYoutube)) {
            socWrapPass = 0;
            socScrollPos = 0;
            socState = NP_SCROLL_WRAP;
          } else {
            socState = NP_SCROLL_RIGHT;
          }
          socLastScrollMs = now;
        }
        break;
      case NP_SCROLL_WRAP: {
        if (now - socLastScrollMs >= spd(SPD_YOUTUBE)) {
          socLastScrollMs = now;
          socScrollPos++;
          if (socScrollPos >= socColCount) {
            socWrapPass++;
            if (socWrapPass >= SCROLL_WRAP_PASSES) {
              advanceSlot();
              serviceHttp();
              if (tileLoopSuspended()) return;
              return;
            }
            socScrollPos = -((hideIconYoutube || scrollIconInBuffer(scrollTypeYoutube)) ? 32 : PRESSURE_TEXT_COLS);
          }
          socialDrawAtPos(socScrollPos);
        }
        break;
      }
      case NP_SCROLL_RIGHT: {
        int maxPos = socColCount - ((hideIconYoutube || scrollIconInBuffer(scrollTypeYoutube)) ? 32 : PRESSURE_TEXT_COLS);
        if (maxPos <= 0) {
          socState = NP_PAUSE_SHORT;
          socPauseMs = now;
          break;
        }
        if (now - socLastScrollMs >= spd(SPD_YOUTUBE)) {
          socLastScrollMs = now;
          socScrollPos++;
          socialDrawAtPos(socScrollPos);
          if (socScrollPos >= maxPos) {
            socScrollPos = maxPos;
            socState = NP_PAUSE_AFTER_RIGHT;
            socPauseMs = now;
          }
        }
        break;
      }
      case NP_PAUSE_AFTER_RIGHT:
        if (now - socPauseMs >= NP_PAUSE_MS) {
          socState = NP_SCROLL_LEFT;
          socLastScrollMs = now;
        }
        break;
      case NP_SCROLL_LEFT:
        if (now - socLastScrollMs >= spd(SPD_YOUTUBE)) {
          socLastScrollMs = now;
          socScrollPos--;
          if (socScrollPos <= 0) {
            socScrollPos = 0;
            socialDrawAtPos(0);
            socState = NP_PAUSE_BEFORE_NEXT;
            socPauseMs = now;
          } else {
            socialDrawAtPos(socScrollPos);
          }
        }
        break;
      case NP_PAUSE_BEFORE_NEXT:
        if (now - socPauseMs >= NP_PAUSE_MS) {
          advanceSlot();
          serviceHttp();
          if (tileLoopSuspended()) return;
          return;
        }
        break;
      case NP_PAUSE_SHORT:
        if (now - socPauseMs >= 4000UL) {
          advanceSlot();
          serviceHttp();
          if (tileLoopSuspended()) return;
          return;
        }
        break;
    }
    serviceHttp();
    if (tileLoopSuspended()) return;
    return;
  }


  // MEMENTO 
  if (cur.id == ITEM_MEMENTO) {
    unsigned long now = millis();
    switch (mementoState) {
      case NP_SHOW_START:
        break;
      case NP_PAUSE_BEFORE_RIGHT:
        if (now - mementoPauseMs >= NP_PAUSE_MS) {
          if (scrollIsWrap(scrollTypeReminder)) {
            mementoWrapPass = 0;
            mementoScrollPos = 0;
            mementoState = NP_SCROLL_WRAP;
          } else {
            mementoState = NP_SCROLL_RIGHT;
          }
          mementoLastScrollMs = now;
        }
        break;
      case NP_SCROLL_WRAP: {
        if (now - mementoLastScrollMs >= spd(SPD_REMINDER)) {
          mementoLastScrollMs = now;
          mementoScrollPos++;
          if (mementoScrollPos >= mementoColCount) {
            mementoWrapPass++;
            if (mementoWrapPass >= SCROLL_WRAP_PASSES) {
              advanceSlot();
              serviceHttp();
              if (tileLoopSuspended()) return;
              return;
            }
            mementoScrollPos = -((hideIconReminder || scrollIconInBuffer(scrollTypeReminder)) ? 32 : NP_TEXT_COLS);
          }
          mementoDrawAtPos(mementoScrollPos);
        }
        break;
      }
      case NP_SCROLL_RIGHT: {
        int maxPos = mementoColCount - ((hideIconReminder || scrollIconInBuffer(scrollTypeReminder)) ? 32 : NP_TEXT_COLS);
        if (maxPos <= 0) {
          mementoState = NP_PAUSE_SHORT;
          mementoPauseMs = now;
          break;
        }
        if (now - mementoLastScrollMs >= spd(SPD_REMINDER)) {
          mementoLastScrollMs = now;
          mementoScrollPos++;
          mementoDrawAtPos(mementoScrollPos);
          if (mementoScrollPos >= maxPos) {
            mementoScrollPos = maxPos;
            mementoState = NP_PAUSE_AFTER_RIGHT;
            mementoPauseMs = now;
          }
        }
        break;
      }
      case NP_PAUSE_AFTER_RIGHT:
        if (now - mementoPauseMs >= NP_PAUSE_MS) {
          mementoState = NP_SCROLL_LEFT;
          mementoLastScrollMs = now;
        }
        break;
      case NP_SCROLL_LEFT:
        if (now - mementoLastScrollMs >= spd(SPD_REMINDER)) {
          mementoLastScrollMs = now;
          mementoScrollPos--;
          if (mementoScrollPos <= 0) {
            mementoScrollPos = 0;
            mementoDrawAtPos(0);
            mementoState = NP_PAUSE_BEFORE_NEXT;
            mementoPauseMs = now;
          } else {
            mementoDrawAtPos(mementoScrollPos);
          }
        }
        break;
      case NP_PAUSE_BEFORE_NEXT:
        if (now - mementoPauseMs >= NP_PAUSE_MS) {
          advanceSlot();
          serviceHttp();
          if (tileLoopSuspended()) return;
          return;
        }
        break;
      case NP_PAUSE_SHORT:
        if (now - mementoPauseMs >= 4000UL) {
          advanceSlot();
          serviceHttp();
          if (tileLoopSuspended()) return;
          return;
        }
        break;
    }
    serviceHttp();
    if (tileLoopSuspended()) return;
    return;
  }

  serviceHttp();
  if (tileLoopSuspended()) return;

  unsigned long nowMs = millis();

  static unsigned long lastBrightCheck = 0;
  if (nowMs - lastBrightCheck >= 1000UL) {
    lastBrightCheck = nowMs;
    applyBrightness();
  }

  // Both fetches below only kick off a background task and return
  // immediately (see weatherFetch()/currencyFetch() definitions) - they
  // no longer block loop() while the HTTP request is in flight.
  // Both are gated on the tile still being in the manager: a removed tile has
  // no row to show the answer on, and each refresh is an HTTPS request plus an
  // 8 KB task. The poll calls stay unconditional so a fetch already in flight
  // when the tile was removed still gets collected instead of leaking its flag.
  if (tileInManager(ITEM_WEATHER) && strlen(weatherApiKey) > 0 &&
      (lastWeatherFetch == 0 || nowMs - lastWeatherFetch >= WEATHER_FETCH_INTERVAL_MS)) {
    weatherFetch();
  }
  weatherFetchPoll();

  if (tileInManager(ITEM_CURRENCY) &&
      (lastCurrencyFetch == 0 || nowMs - lastCurrencyFetch >= CURRENCY_FETCH_INTERVAL_MS)) {
    currencyFetch();
  }
  currencyFetchPoll();

  socialTickFetch();
  socialFetchPoll();

  settingsFlushTick();
  bmpHealthTick();
  tempSampleTick();
  pressureSampleTick();

  nowMs = millis();

  switch (cur.id) {
    case ITEM_HOUR:

      if (nowMs - gLastStaticDrawMs >= 200) {
        gLastStaticDrawMs = nowMs;
        drawHour();
      }
      break;
    case ITEM_HOURWEEK:
      if (nowMs - gLastStaticDrawMs >= 200) {
        gLastStaticDrawMs = nowMs;
        drawHourWeekday();
      }
      break;
    case ITEM_DATE: {

      if (!gStaticDrawDone) {
        gStaticDrawDone = dateInit();
      }

      // dateState stays NP_SHOW_START until dateInit() starts the scroll, and
      // dateNeedsScroll survives from the previous time this tile was shown -
      // so the two can disagree. Entering the state machine on that combination
      // lands on `default:` and returns out of loop() on every pass, without
      // ever reaching the slot-duration check below: the tile could never hand
      // over. Falling through instead keeps the rotation going whatever
      // happened to the draw.
      if (dateNeedsScroll && dateState != NP_SHOW_START) {
        unsigned long now = millis();
        unsigned long halfSlot = (unsigned long)(cur.durationSec / 2) * 1000UL;
        if (halfSlot < 1000UL) halfSlot = 1000UL;
        int dateEffTextCols = (hideIconDate || scrollIconInBuffer(scrollTypeDate)) ? 32 : DATE_TEXT_COLS;
        int maxScroll = dateColCount - dateEffTextCols;
        if (maxScroll < 0) maxScroll = 0;
        switch (dateState) {
          case NP_PAUSE_BEFORE_RIGHT:

            if (now - datePauseMs >= halfSlot) {
              if (scrollIsWrap(scrollTypeDate)) {
                dateWrapPass = 0;
                dateScrollPos = 0;
                dateState = NP_SCROLL_WRAP;
              } else {
                dateState = NP_SCROLL_RIGHT;
              }
              dateLastScrollMs = now;
            }
            break;
          case NP_SCROLL_WRAP:
            if (now - dateLastScrollMs >= spd(SPD_DATE)) {
              dateLastScrollMs = now;
              dateScrollPos++;
              if (dateScrollPos >= dateColCount) {
                dateWrapPass++;
                if (dateWrapPass >= SCROLL_WRAP_PASSES) {
                  advanceSlot();
                  serviceHttp();
                  if (tileLoopSuspended()) return;
                  return;
                }
                dateScrollPos = -dateEffTextCols;
              }
              dateDrawAtPos(dateScrollPos);
            }
            break;
          case NP_SCROLL_RIGHT:
            if (now - dateLastScrollMs >= spd(SPD_DATE)) {
              dateLastScrollMs = now;
              dateScrollPos++;
              dateDrawAtPos(dateScrollPos);
              if (dateScrollPos >= maxScroll) {
                dateScrollPos = maxScroll;
                dateState = NP_PAUSE_AFTER_RIGHT;
                datePauseMs = now;
              }
            }
            break;
          case NP_PAUSE_AFTER_RIGHT:
            if (now - datePauseMs >= NP_PAUSE_MS) {
              dateState = NP_SCROLL_LEFT;
              dateLastScrollMs = now;
            }
            break;
          case NP_SCROLL_LEFT:
            if (now - dateLastScrollMs >= spd(SPD_DATE)) {
              dateLastScrollMs = now;
              dateScrollPos--;
              if (dateScrollPos <= 0) {
                dateScrollPos = 0;
                dateDrawAtPos(0);
                dateState = NP_PAUSE_BEFORE_NEXT;
                datePauseMs = now;
              } else {
                dateDrawAtPos(dateScrollPos);
              }
            }
            break;
          case NP_PAUSE_BEFORE_NEXT:

            if (now - datePauseMs >= halfSlot) {
              advanceSlot();
              serviceHttp();
              if (tileLoopSuspended()) return;
              return;
            }
            break;
          default: break;
        }

        serviceHttp();
        if (tileLoopSuspended()) return;
        return;
      }
      break;
    }
    case ITEM_TEMP: {

      if (!gStaticDrawDone) {
        float tf;
        if (bmpReadTempC(tf)) lastTemp = (int)round(tf);
        gStaticDrawDone = true;
        gTempShownValue = lastTemp;
        tempInit(lastTemp);
      } else if (gTempShownValue == TEMP_NO_READING && lastTemp != TEMP_NO_READING) {
        // The "--" placeholder is on screen and the sensor just answered.
        // Only re-init in this direction, so a normal reading changing by a
        // degree never restarts a scroll that is already running.
        gTempShownValue = lastTemp;
        tempInit(lastTemp);
      }

      if (tempNeedsScroll) {
        unsigned long now = millis();
        unsigned long halfSlot = (unsigned long)(cur.durationSec / 2) * 1000UL;
        if (halfSlot < 1000UL) halfSlot = 1000UL;
        int tempEffTextCols = (hideIconTemp || scrollIconInBuffer(scrollTypeTemp)) ? 32 : TEMP_TEXT_COLS;
        int maxScroll = tempColCount - tempEffTextCols;
        if (maxScroll < 0) maxScroll = 0;
        switch (tempState) {
          case NP_PAUSE_BEFORE_RIGHT:

            if (now - tempPauseMs >= halfSlot) {
              if (scrollIsWrap(scrollTypeTemp)) {
                tempWrapPass = 0;
                tempScrollPos = 0;
                tempState = NP_SCROLL_WRAP;
              } else {
                tempState = NP_SCROLL_RIGHT;
              }
              tempLastScrollMs = now;
            }
            break;
          case NP_SCROLL_WRAP:
            if (now - tempLastScrollMs >= spd(SPD_TEMP)) {
              tempLastScrollMs = now;
              tempScrollPos++;
              if (tempScrollPos >= tempColCount) {
                tempWrapPass++;
                if (tempWrapPass >= SCROLL_WRAP_PASSES) {
                  advanceSlot();
                  serviceHttp();
                  if (tileLoopSuspended()) return;
                  return;
                }
                tempScrollPos = -tempEffTextCols;
              }
              tempDrawAtPos(tempScrollPos);
            }
            break;
          case NP_SCROLL_RIGHT:
            if (now - tempLastScrollMs >= spd(SPD_TEMP)) {
              tempLastScrollMs = now;
              tempScrollPos++;
              tempDrawAtPos(tempScrollPos);
              if (tempScrollPos >= maxScroll) {
                tempScrollPos = maxScroll;
                tempState = NP_PAUSE_AFTER_RIGHT;
                tempPauseMs = now;
              }
            }
            break;
          case NP_PAUSE_AFTER_RIGHT:
            if (now - tempPauseMs >= NP_PAUSE_MS) {
              tempState = NP_SCROLL_LEFT;
              tempLastScrollMs = now;
            }
            break;
          case NP_SCROLL_LEFT:
            if (now - tempLastScrollMs >= spd(SPD_TEMP)) {
              tempLastScrollMs = now;
              tempScrollPos--;
              if (tempScrollPos <= 0) {
                tempScrollPos = 0;
                tempDrawAtPos(0);
                tempState = NP_PAUSE_BEFORE_NEXT;
                tempPauseMs = now;
              } else {
                tempDrawAtPos(tempScrollPos);
              }
            }
            break;
          case NP_PAUSE_BEFORE_NEXT:

            if (now - tempPauseMs >= halfSlot) {
              advanceSlot();
              serviceHttp();
              if (tileLoopSuspended()) return;
              return;
            }
            break;
          default: break;
        }

        serviceHttp();
        if (tileLoopSuspended()) return;
        return;
      }
      break;
    }
    case ITEM_PRESSURE: {

      if (!gStaticDrawDone) {
        pressureSampleTick();
        gStaticDrawDone = true;
        pressureInit((int)round(lastPressureHpa));
      }

      if (pressureNeedsScroll) {
        unsigned long now = millis();
        unsigned long halfSlot = (unsigned long)(cur.durationSec / 2) * 1000UL;
        if (halfSlot < 1000UL) halfSlot = 1000UL;
        int pressureEffTextCols = (hideIconPressure || scrollIconInBuffer(scrollTypePressure)) ? 32 : PRESSURE_TEXT_COLS;
        int maxScroll = pressureColCount - pressureEffTextCols;
        if (maxScroll < 0) maxScroll = 0;
        switch (pressureState) {
          case NP_PAUSE_BEFORE_RIGHT:
            if (now - pressurePauseMs >= halfSlot) {
              if (scrollIsWrap(scrollTypePressure)) {
                pressureWrapPass = 0;
                pressureScrollPos = 0;
                pressureState = NP_SCROLL_WRAP;
              } else {
                pressureState = NP_SCROLL_RIGHT;
              }
              pressureLastScrollMs = now;
            }
            break;
          case NP_SCROLL_WRAP:
            if (now - pressureLastScrollMs >= spd(SPD_PRESSURE)) {
              pressureLastScrollMs = now;
              pressureScrollPos++;
              if (pressureScrollPos >= pressureColCount) {
                pressureWrapPass++;
                if (pressureWrapPass >= SCROLL_WRAP_PASSES) {
                  advanceSlot();
                  serviceHttp();
                  if (tileLoopSuspended()) return;
                  return;
                }
                pressureScrollPos = -pressureEffTextCols;
              }
              pressureDrawAtPos(pressureScrollPos);
            }
            break;
          case NP_SCROLL_RIGHT:
            if (now - pressureLastScrollMs >= spd(SPD_PRESSURE)) {
              pressureLastScrollMs = now;
              pressureScrollPos++;
              pressureDrawAtPos(pressureScrollPos);
              if (pressureScrollPos >= maxScroll) {
                pressureScrollPos = maxScroll;
                pressureState = NP_PAUSE_AFTER_RIGHT;
                pressurePauseMs = now;
              }
            }
            break;
          case NP_PAUSE_AFTER_RIGHT:
            if (now - pressurePauseMs >= NP_PAUSE_MS) {
              pressureState = NP_SCROLL_LEFT;
              pressureLastScrollMs = now;
            }
            break;
          case NP_SCROLL_LEFT:
            if (now - pressureLastScrollMs >= spd(SPD_PRESSURE)) {
              pressureLastScrollMs = now;
              pressureScrollPos--;
              if (pressureScrollPos <= 0) {
                pressureScrollPos = 0;
                pressureDrawAtPos(0);
                pressureState = NP_PAUSE_BEFORE_NEXT;
                pressurePauseMs = now;
              } else {
                pressureDrawAtPos(pressureScrollPos);
              }
            }
            break;
          case NP_PAUSE_BEFORE_NEXT:
            if (now - pressurePauseMs >= halfSlot) {
              advanceSlot();
              serviceHttp();
              if (tileLoopSuspended()) return;
              return;
            }
            break;
          default: break;
        }
        serviceHttp();
        if (tileLoopSuspended()) return;
        return;
      }
      break;
    }
    case ITEM_SCREENSAVER: {

      if (!ssWaitingAdvance && (nowMs - slotStartMs >= (unsigned long)cur.durationSec * 1000UL)) {
        ssWaitingAdvance = true;
        ssWaitStartMs = nowMs;
      }
      ssTick();
      return;
    }
  }

  if (nowMs - slotStartMs >= (unsigned long)cur.durationSec * 1000UL) {
    advanceSlot();
  }
}
